ProccyBoi/kiku/Mechanical/concepts/01_Mame_front.png

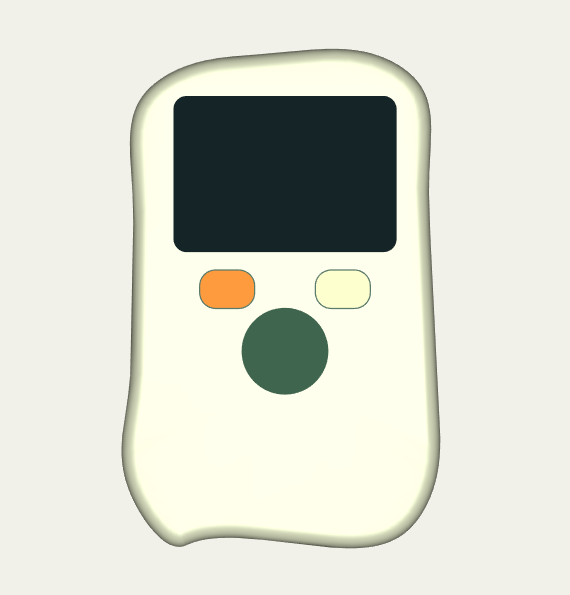
Mechanical/concepts/01_Mame_front.png
