ProccyBoi/kiku/Mechanical/concepts/01_Mame_rear.png

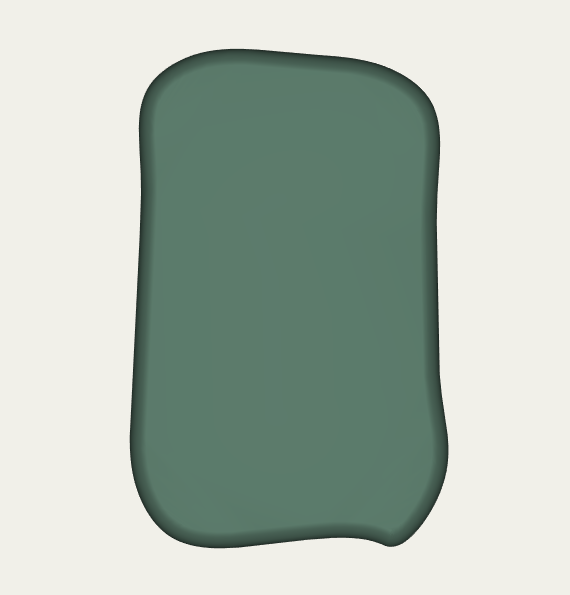
Mechanical/concepts/01_Mame_rear.png
