ProccyBoi/kiku/Mechanical/concepts/01_Mame_side.png

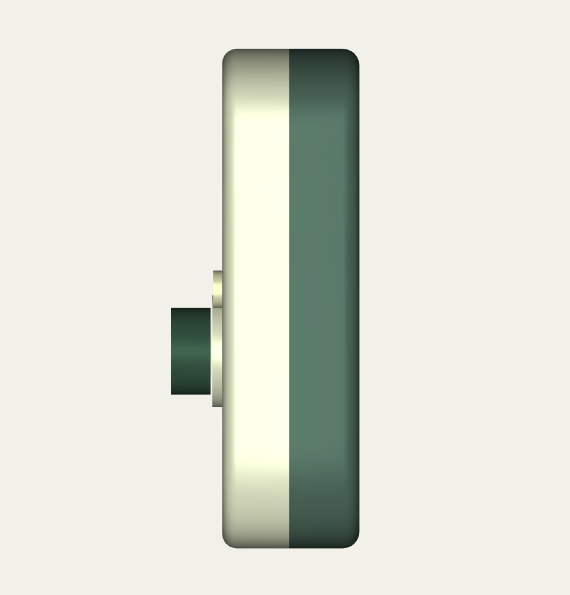
Mechanical/concepts/01_Mame_side.png
