ProccyBoi/kiku/Mechanical/concepts/02_Nagare_front.png

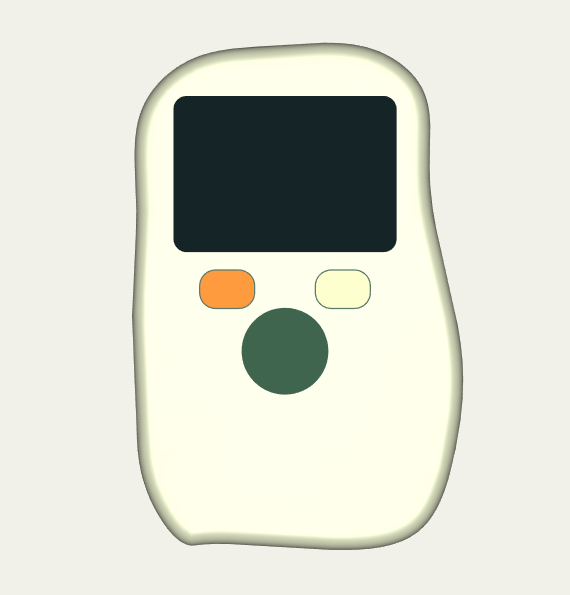
Mechanical/concepts/02_Nagare_front.png
