ProccyBoi/kiku/Mechanical/concepts/02_Nagare_rear.png

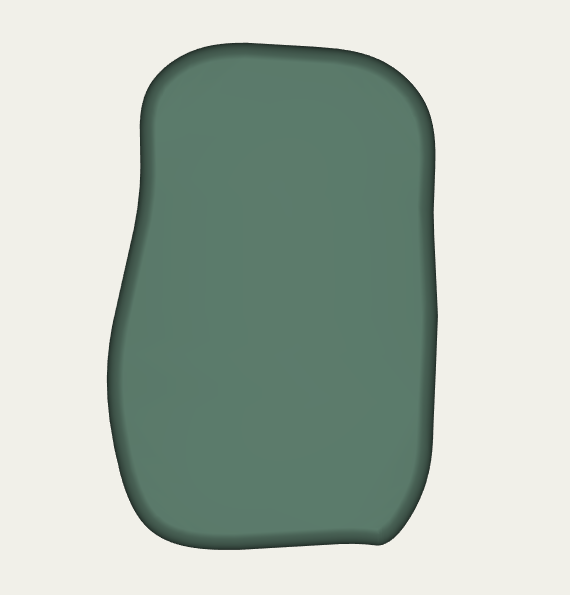
Mechanical/concepts/02_Nagare_rear.png
