ProccyBoi/kiku/Mechanical/concepts/03_Mini_rear.png

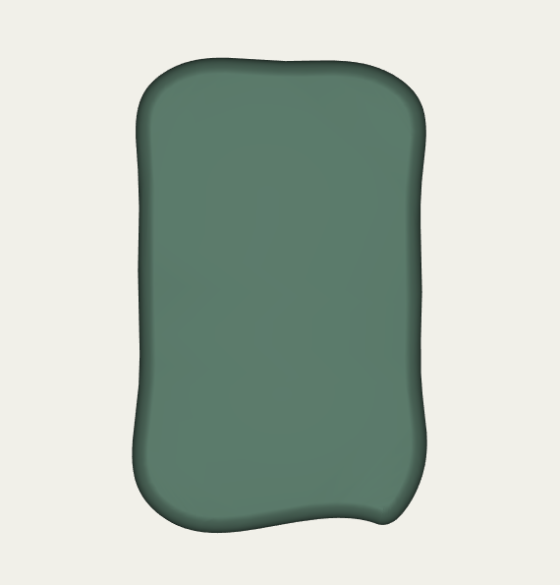
Mechanical/concepts/03_Mini_rear.png
