ProccyBoi/kiku/Mechanical/review/kiku_housing_v1_exploded.png

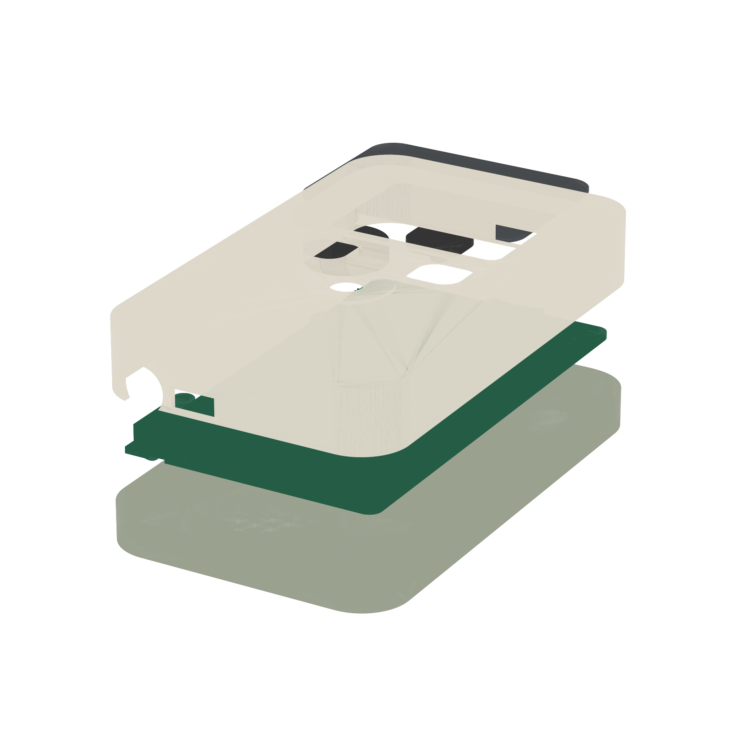
Mechanical/review/kiku_housing_v1_exploded.png
