ProccyBoi/kiku/Mechanical/review/kiku_housing_v1_front_3q.png

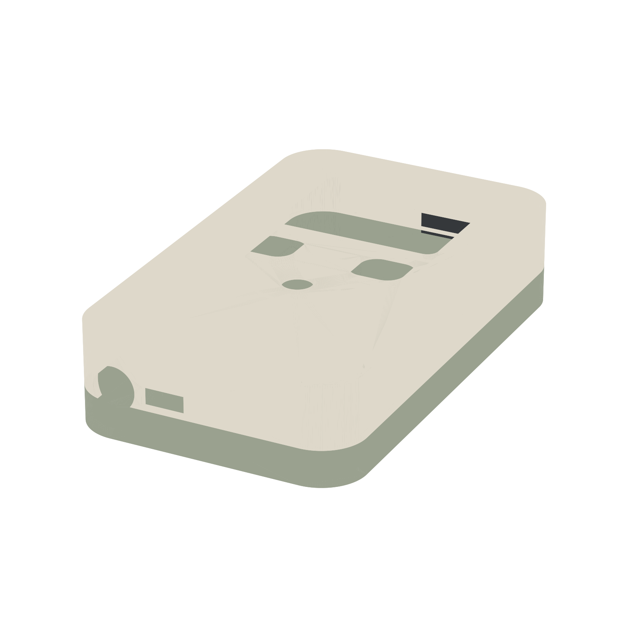
Mechanical/review/kiku_housing_v1_front_3q.png
