ProccyBoi/kiku/Mechanical/review/kiku_housing_v1_rear_3q.png

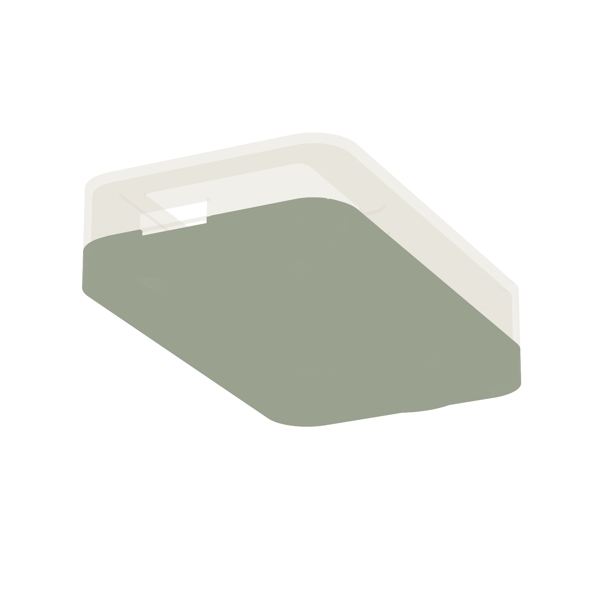
Mechanical/review/kiku_housing_v1_rear_3q.png
