ProccyBoi/kiku/Mechanical/review/kiku_housing_v6_stand_open.png

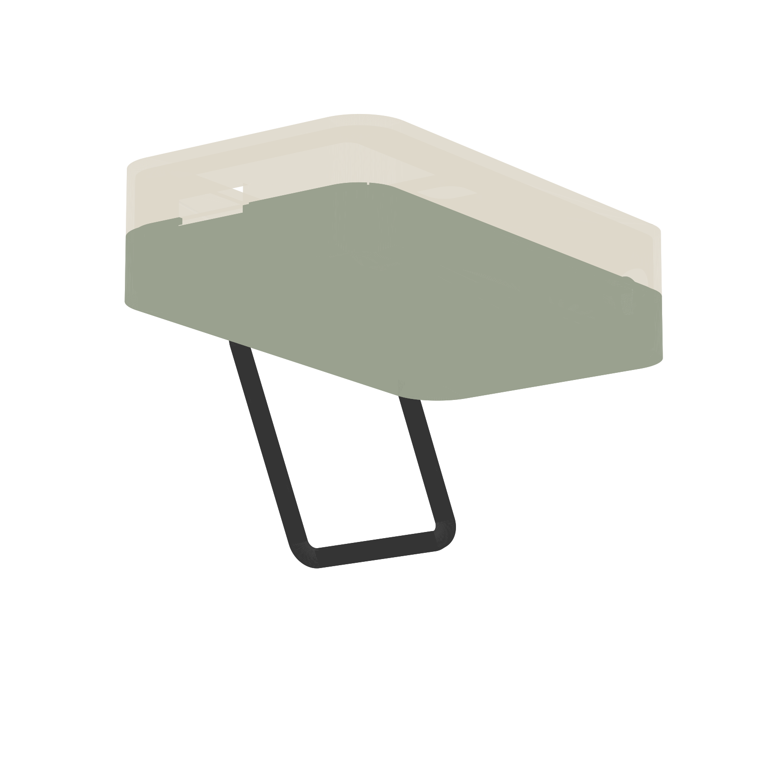
Mechanical/review/kiku_housing_v6_stand_open.png
