ProccyBoi/kiku/Mechanical/review/kiku_housing_v7_controls_closeup.png

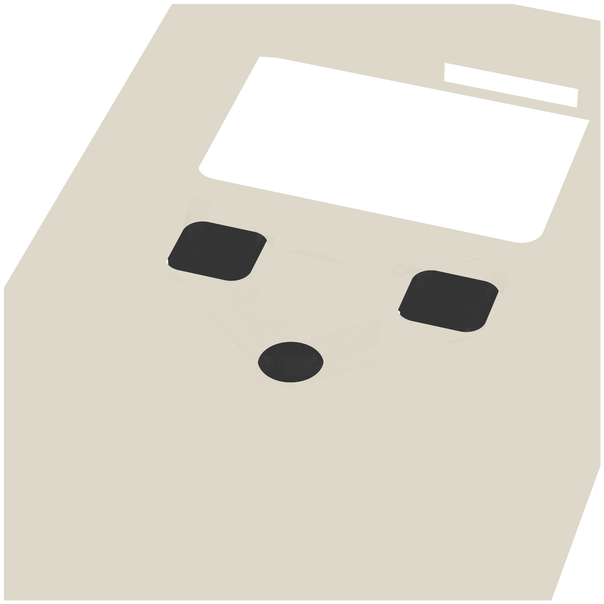
Mechanical/review/kiku_housing_v7_controls_closeup.png
