ProccyBoi/kiku/Mechanical/review/P1_antenna_route.png

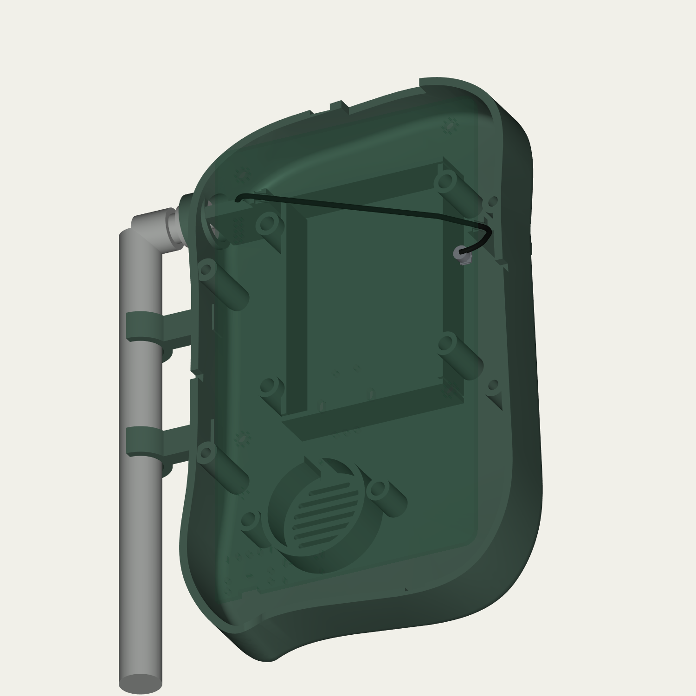
Mechanical/review/P1_antenna_route.png
