ProccyBoi/kiku/Mechanical/exports/P0/front_shell.step

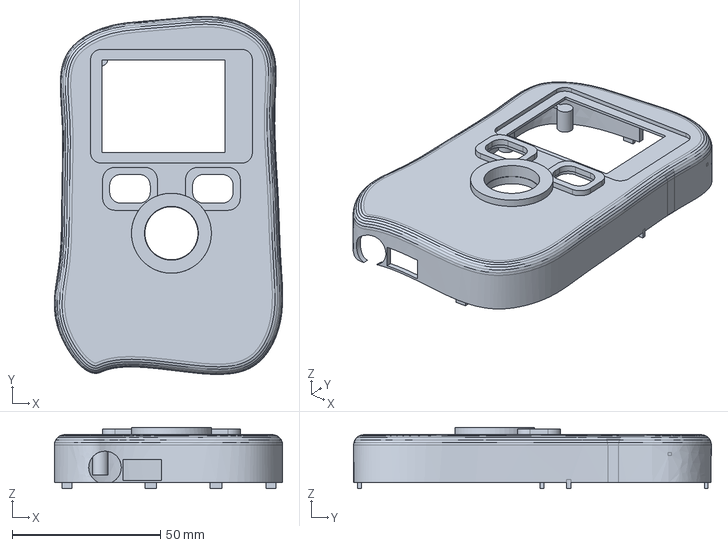
[picture p42: CAD file, 2026-09-17]
Mechanical/exports/P0/front_shell.step
77.1 x 120.9 x 20.6 mm
