ProccyBoi/kiku/Mechanical/concepts/03_Mini_front_shell.stl

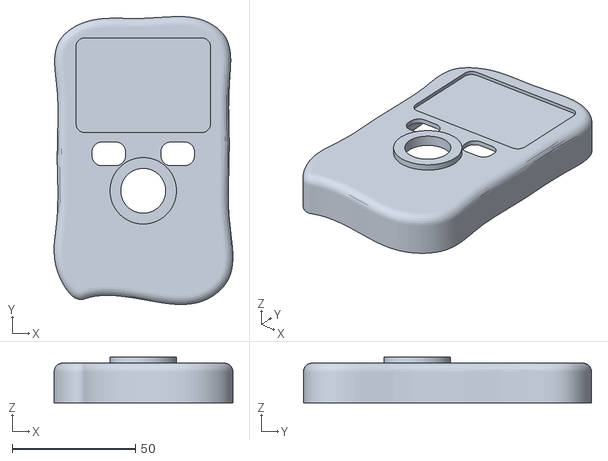
[picture p43: CAD file, 2026-09-17]
Mechanical/concepts/03_Mini_front_shell.stl
72.7 x 117.0 x 18.6
