ProccyBoi/kiku/Mechanical/exports/P0/encoder_knob.step

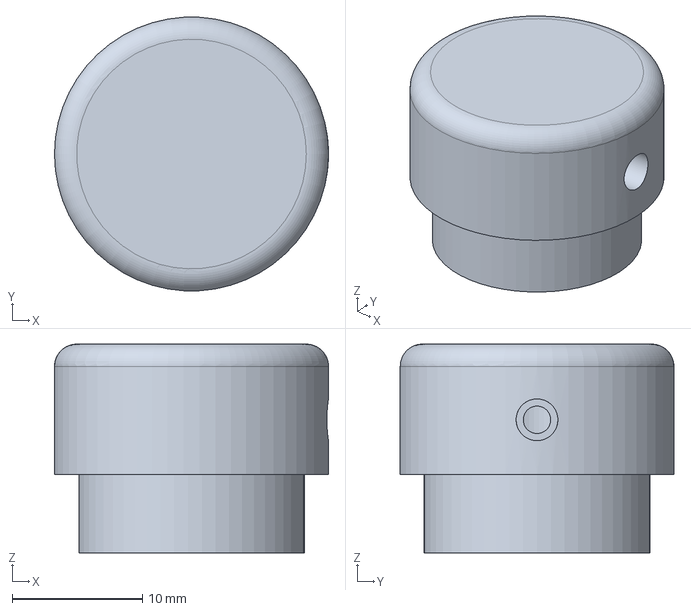
[picture p44: CAD file, 2026-09-17]
Mechanical/exports/P0/encoder_knob.step
21.0 x 21.0 x 16.0 mm
