ProccyBoi/kiku/Mechanical/concepts/02_Nagare_front_shell.stl

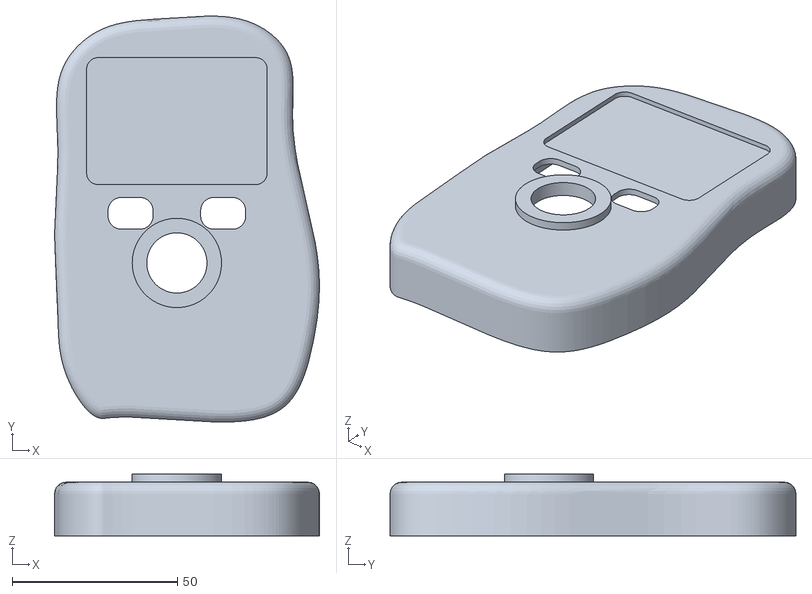
[picture p45: CAD file, 2026-09-17]
Mechanical/concepts/02_Nagare_front_shell.stl
80.1 x 122.7 x 18.6
