ProccyBoi/kiku/Mechanical/exports/kiku_button_right_v8.step

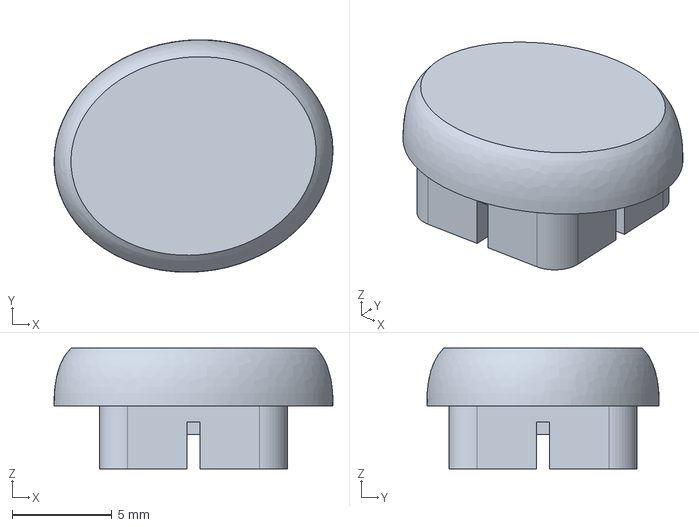
[picture p46: CAD file, 2026-09-17]
Mechanical/exports/kiku_button_right_v8.step
14.0 x 11.6 x 6.05 mm
