ProccyBoi/kiku/Mechanical/concepts/03_Mini.step

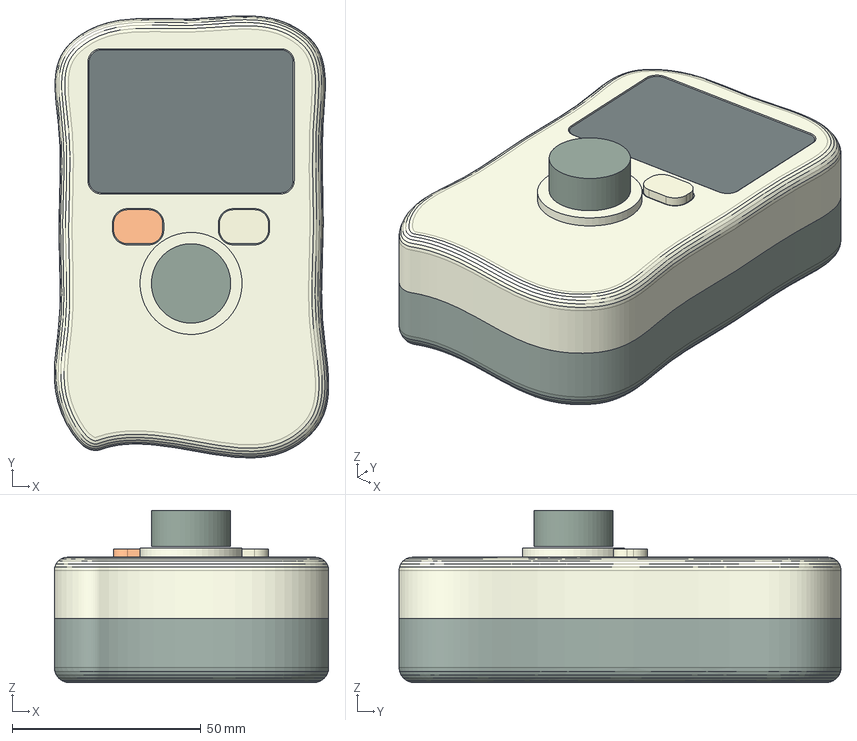
[picture p47: CAD file, 2026-09-17]
Mechanical/concepts/03_Mini.step
72.6 x 116.9 x 45.6 mm
front_shell
rear_shell
lens
button_left
button_right
encoder_knob
