ProccyBoi/kiku/Mechanical/concepts/01_Mame_rear_shell.stl

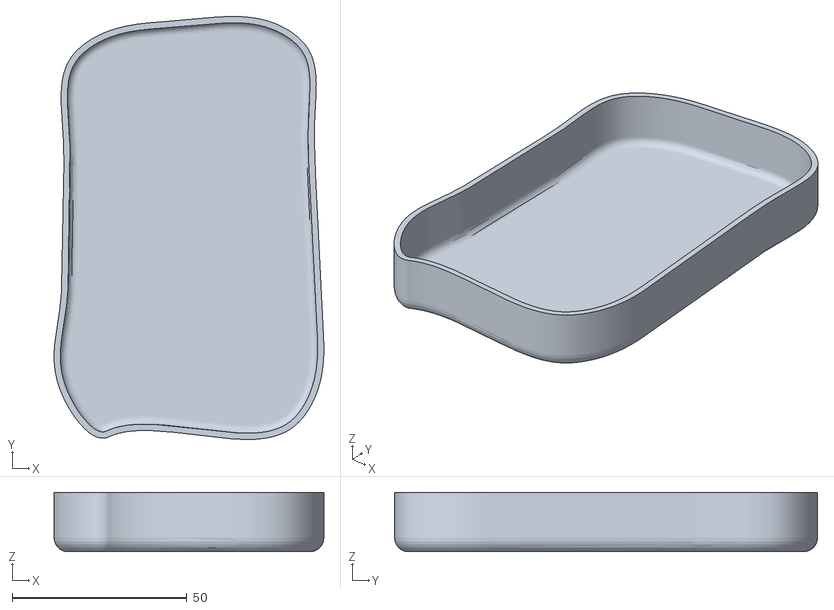
[picture p48: CAD file, 2026-09-17]
Mechanical/concepts/01_Mame_rear_shell.stl
77.1 x 120.9 x 17.0
