ProccyBoi/kiku/Mechanical/exports/kiku_front_shell_C49247039_v5.step

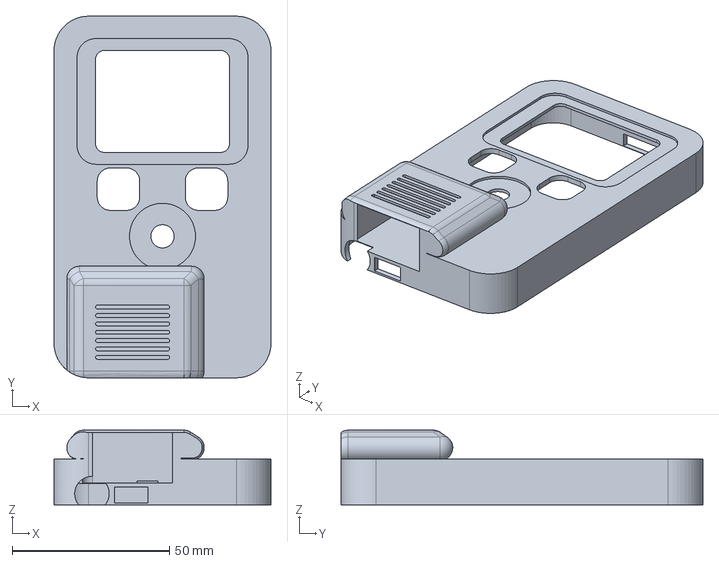
[picture p49: CAD file, 2026-09-17]
Mechanical/exports/kiku_front_shell_C49247039_v5.step
69.0 x 115.0 x 23.7 mm
