ProccyBoi/kiku/Mechanical/concepts/03_Mini_rear_shell.stl

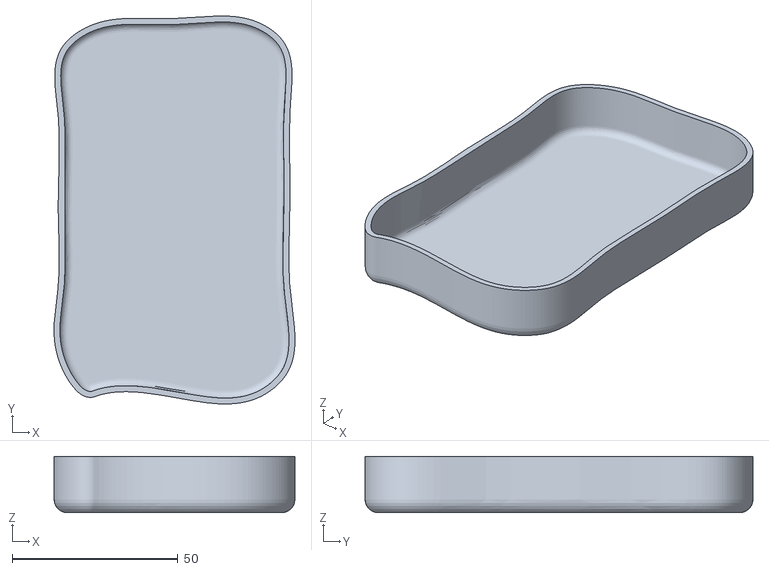
[picture p50: CAD file, 2026-09-17]
Mechanical/concepts/03_Mini_rear_shell.stl
72.7 x 117.0 x 17.0
