ProccyBoi/kiku/Mechanical/concepts/03_Mini_encoder_knob.stl

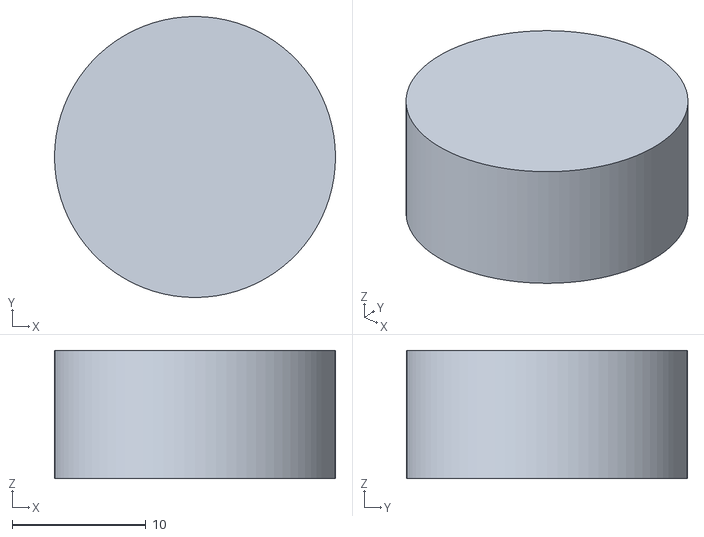
[picture p51: CAD file, 2026-09-17]
Mechanical/concepts/03_Mini_encoder_knob.stl
21.0 x 21.0 x 9.60
