ProccyBoi/kiku/Mechanical/exports/kiku_screen_lens_v8.step

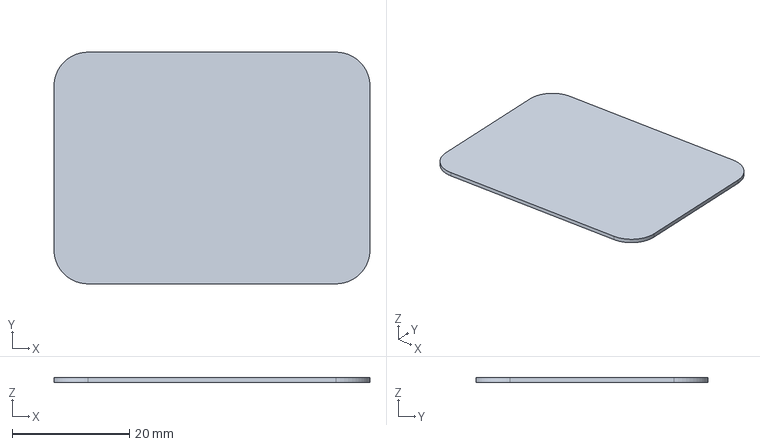
[picture p52: CAD file, 2026-09-17]
Mechanical/exports/kiku_screen_lens_v8.step
54.0 x 39.6 x 0.8 mm
