ProccyBoi/kiku/Mechanical/concepts/02_Nagare.step

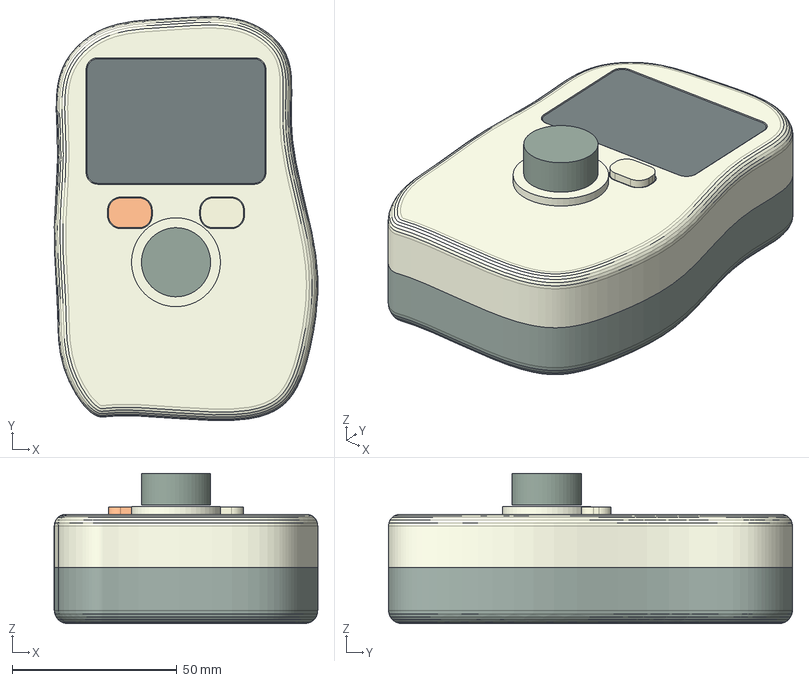
[picture p54: CAD file, 2026-09-17]
Mechanical/concepts/02_Nagare.step
80.0 x 122.7 x 45.6 mm
front_shell
rear_shell
lens
button_left
button_right
encoder_knob
