ProccyBoi/kiku/Mechanical/exports/P1/display_carrier.step

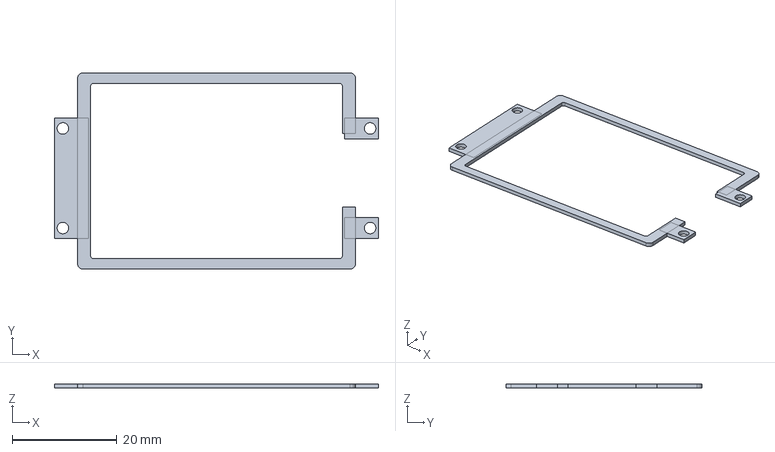
[picture p55: CAD file, 2026-09-17]
Mechanical/exports/P1/display_carrier.step
61.8 x 37.4 x 0.8 mm
