ProccyBoi/kiku/Mechanical/exports/P1/speaker_rear_foam.step

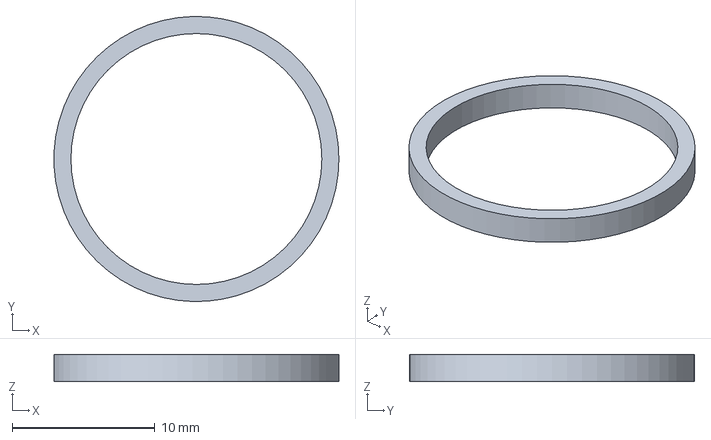
[picture p56: CAD file, 2026-09-17]
Mechanical/exports/P1/speaker_rear_foam.step
20.0 x 20.0 x 1.90 mm
