ProccyBoi/kiku/Mechanical/exports/kiku_speaker_C49247039_envelope_v5.step

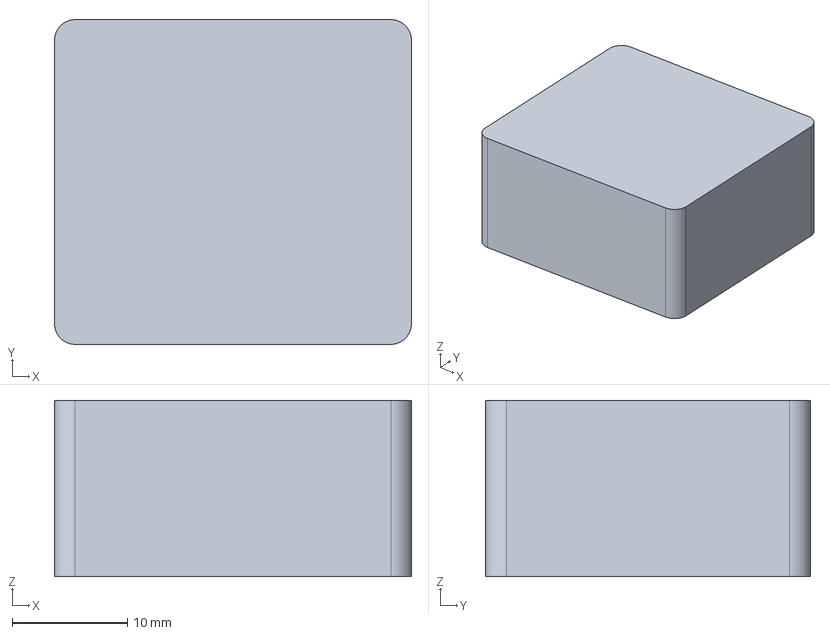
[picture p57: CAD file, 2026-09-17]
Mechanical/exports/kiku_speaker_C49247039_envelope_v5.step
31.0 x 28.2 x 15.3 mm
