ProccyBoi/kiku/Mechanical/exports/P0/battery_foam.step

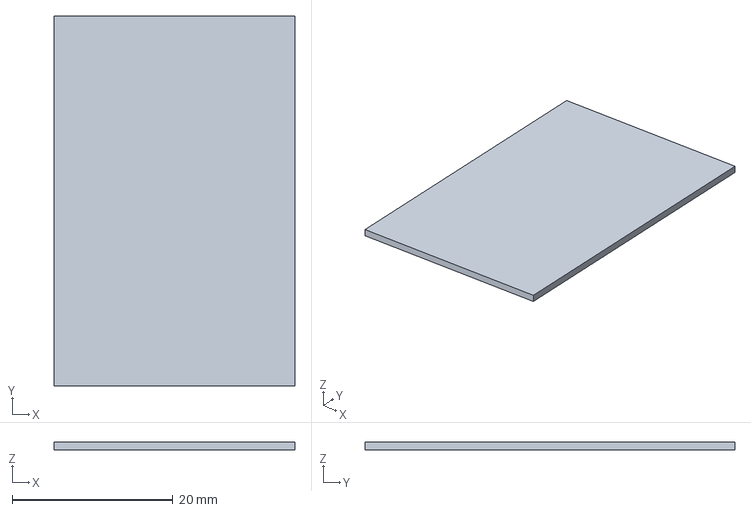
[picture p58: CAD file, 2026-09-17]
Mechanical/exports/P0/battery_foam.step
30.0 x 46.0 x 1.00 mm
