ProccyBoi/kiku/Mechanical/exports/P0/speaker_retainer.step

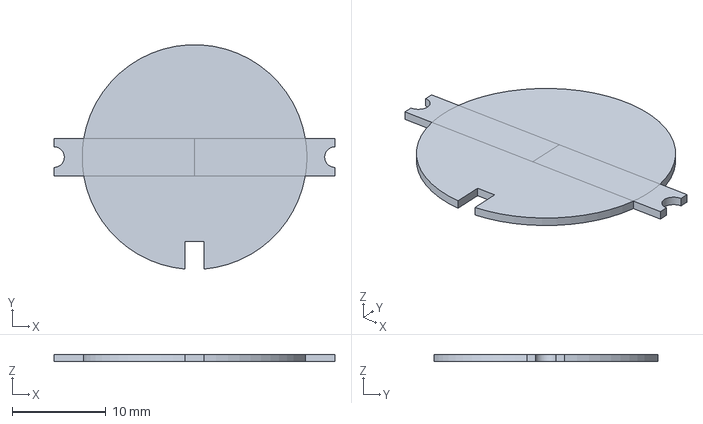
[picture p59: CAD file, 2026-09-17]
Mechanical/exports/P0/speaker_retainer.step
30.0 x 23.9 x 0.8 mm
