ProccyBoi/kiku/Mechanical/exports/kiku_rear_shell_FM_SMA_v5.step

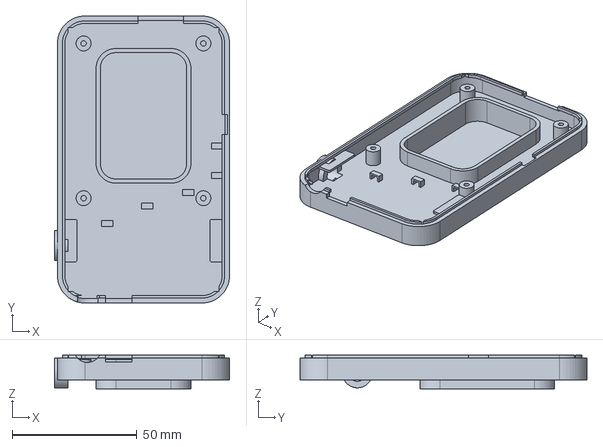
[picture p60: CAD file, 2026-09-17]
Mechanical/exports/kiku_rear_shell_FM_SMA_v5.step
70.2 x 115.0 x 13.5 mm
