ProccyBoi/kiku/Mechanical/exports/P1/speaker_rim_gasket.step

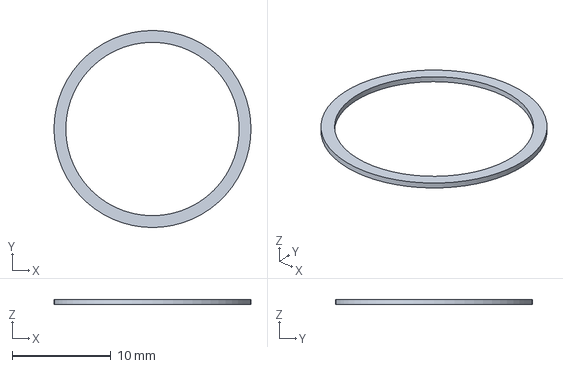
[picture p61: CAD file, 2026-09-17]
Mechanical/exports/P1/speaker_rim_gasket.step
20.0 x 20.0 x 0.5 mm
