ProccyBoi/kiku/Mechanical/exports/P1/Kiku_P1_housing.step

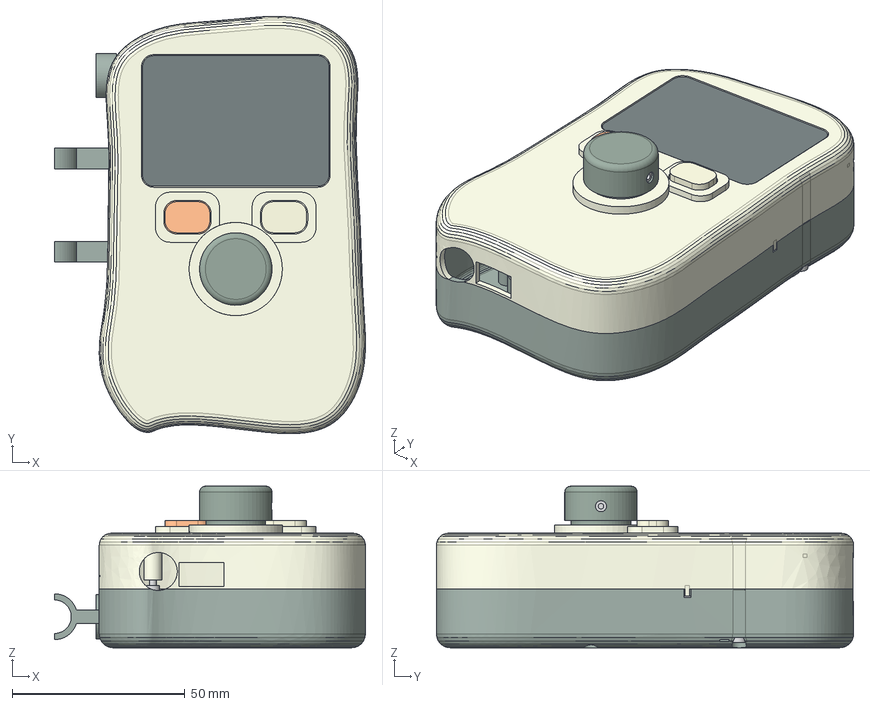
[picture p62: CAD file, 2026-09-17]
Mechanical/exports/P1/Kiku_P1_housing.step
90.1 x 120.9 x 46.8 mm
lcd_screw_0.7_72
lcd_insert_0.7_72
lcd_screw_0.7_91
lcd_insert_0.7_91
lcd_screw_59.3_72
lcd_insert_59.3_72
lcd_screw_59.3_91
lcd_insert_59.3_91
display_carrier
PCB_screw_H5
PCB_insert_H5
PCB_screw_H6
PCB_insert_H6
PCB_screw_H7
PCB_insert_H7
PCB_screw_H8
PCB_insert_H8
case_screw_1
case_insert_1
case_screw_2
case_insert_2
case_screw_3
case_insert_3
case_screw_4
case_insert_4
button_left
button_right
knob_insert
knob_grub_screw
encoder_knob
guard_screw_9.4_51
guard_insert_9.4_51
guard_screw_9.4_89
guard_insert_9.4_89
guard_screw_50.6_51
guard_insert_50.6_51
guard_screw_50.6_89
guard_insert_50.6_89
battery_guard
speaker_screw_3
speaker_insert_3
speaker_screw_33
speaker_insert_33
speaker_retainer
speaker_rim_gasket
speaker_rear_foam
battery_foam
front_shell
rear_shell
lens
