ProccyBoi/kiku/Mechanical/exports/kiku_front_shell_external_speaker_v8.step

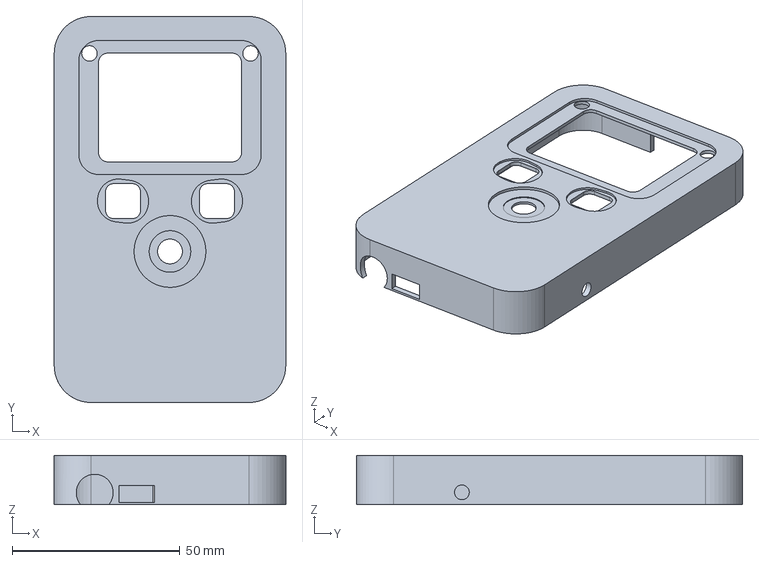
[picture p63: CAD file, 2026-09-17]
Mechanical/exports/kiku_front_shell_external_speaker_v8.step
69.0 x 115.0 x 14.6 mm
