ProccyBoi/kiku/Mechanical/exports/P0/encoder_guide.step

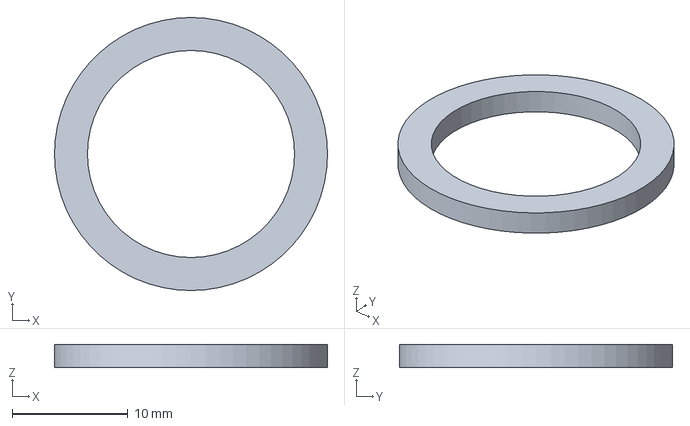
[picture p64: CAD file, 2026-09-17]
Mechanical/exports/P0/encoder_guide.step
23.6 x 23.6 x 2.00 mm
