ProccyBoi/kiku/Mechanical/exports/kiku_speaker_adapter_C50387209_v1.step

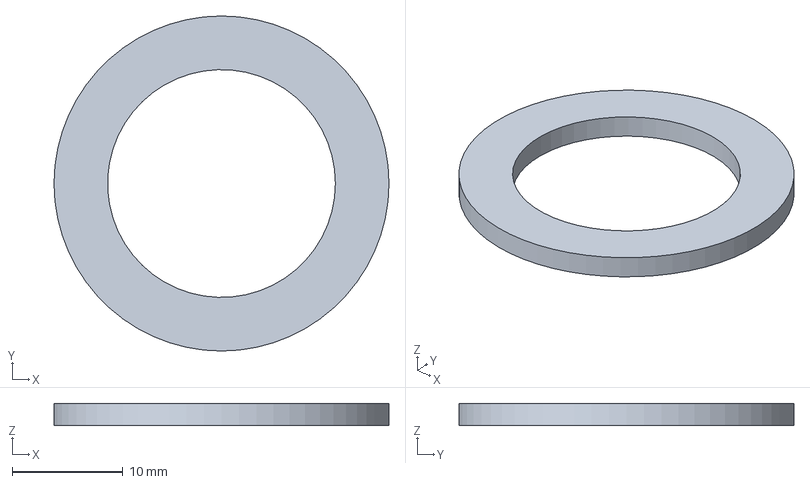
[picture p65: CAD file, 2026-09-17]
Mechanical/exports/kiku_speaker_adapter_C50387209_v1.step
30.3 x 30.3 x 2.00 mm
