ProccyBoi/kiku/Mechanical/exports/P0/rear_shell.step

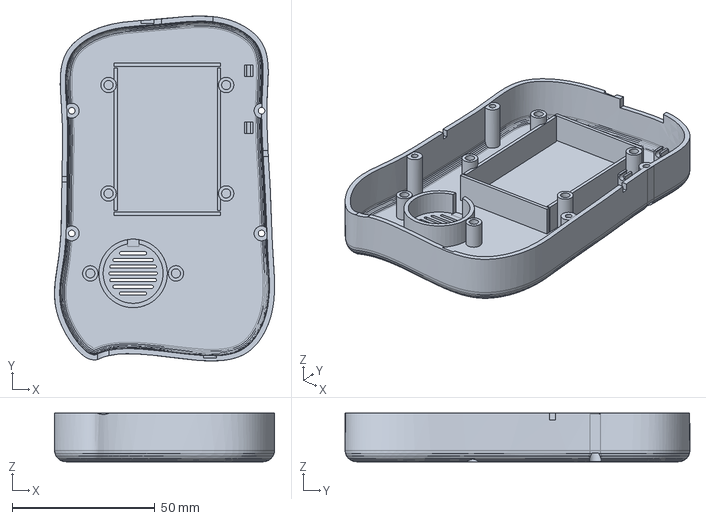
[picture p66: CAD file, 2026-09-17]
Mechanical/exports/P0/rear_shell.step
77.1 x 120.9 x 17.0 mm
