ProccyBoi/kiku/Mechanical/exports/kiku_rear_shell_v1.step

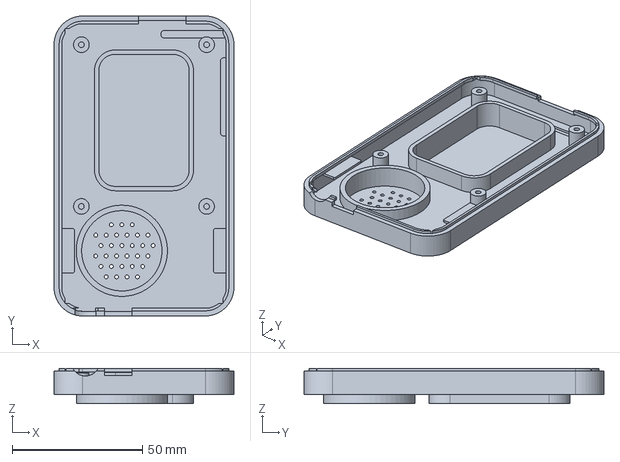
[picture p67: CAD file, 2026-09-17]
Mechanical/exports/kiku_rear_shell_v1.step
69.0 x 115.0 x 13.5 mm
