ProccyBoi/kiku/Mechanical/exports/P0/power_button.step

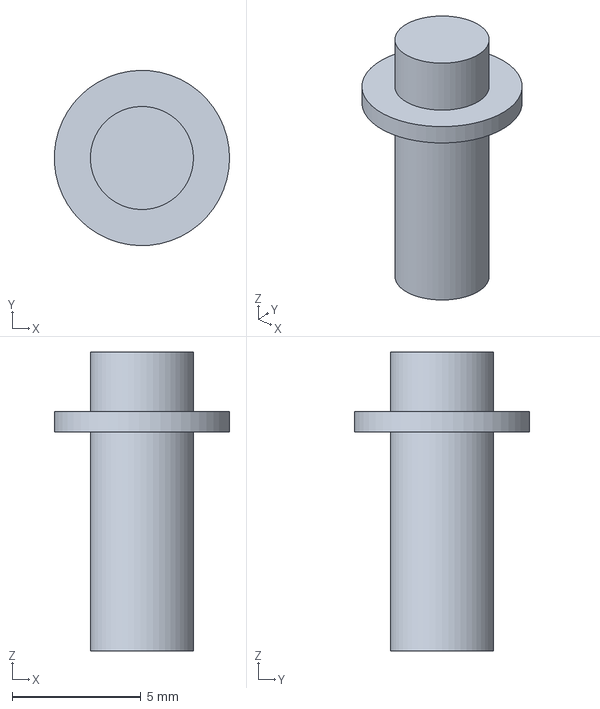
[picture p68: CAD file, 2026-09-17]
Mechanical/exports/P0/power_button.step
6.79 x 6.80 x 11.6 mm
