ProccyBoi/kiku/Mechanical/exports/kiku_encoder_knob_v8.step

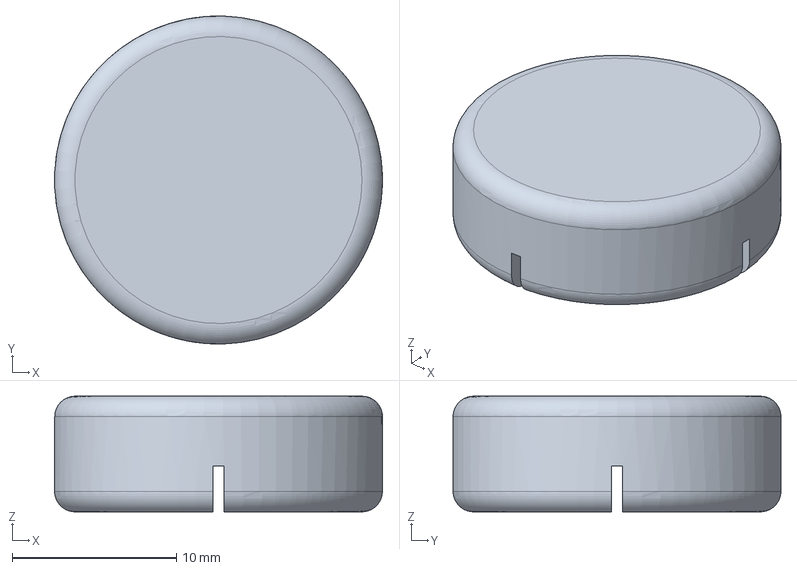
[picture p69: CAD file, 2026-09-17]
Mechanical/exports/kiku_encoder_knob_v8.step
20.0 x 20.0 x 7.05 mm
