ProccyBoi/kiku/Mechanical/exports/kiku_front_shell_C50387209_v2.step

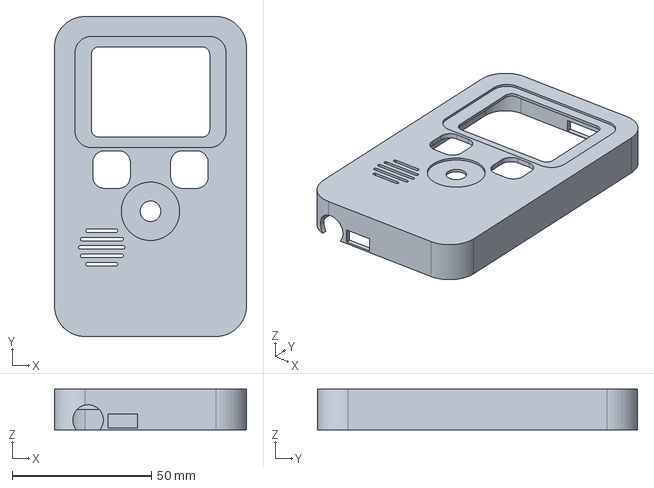
[picture p70: CAD file, 2026-09-17]
Mechanical/exports/kiku_front_shell_C50387209_v2.step
69.0 x 115.0 x 14.6 mm
