ProccyBoi/kiku/Mechanical/exports/kiku_packaging_keepouts_v8.step

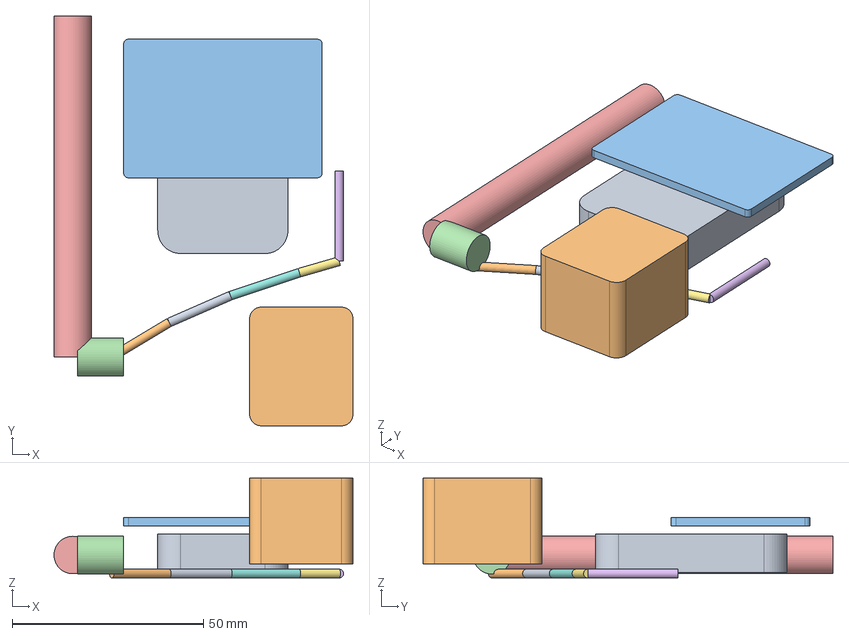
[picture p71: CAD file, 2026-09-17]
Mechanical/exports/kiku_packaging_keepouts_v8.step
78.1 x 107.0 x 26.1 mm
