ProccyBoi/kiku/Mechanical/exports/kiku_kickstand_v8.step

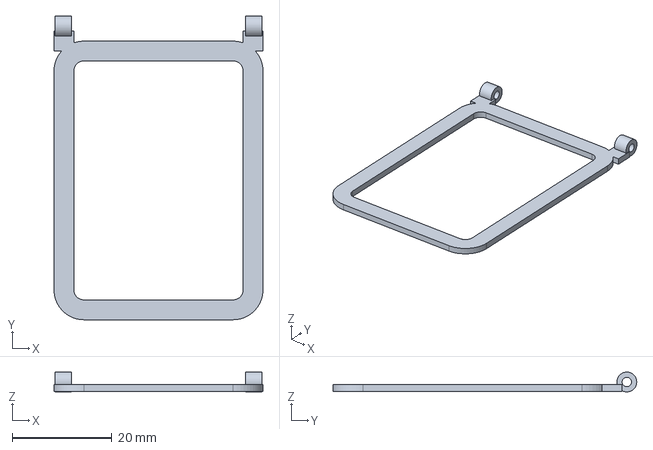
[picture p72: CAD file, 2026-09-17]
Mechanical/exports/kiku_kickstand_v8.step
42.0 x 61.0 x 4.00 mm
