ProccyBoi/kiku/Mechanical/review/P1_assembled_front.png

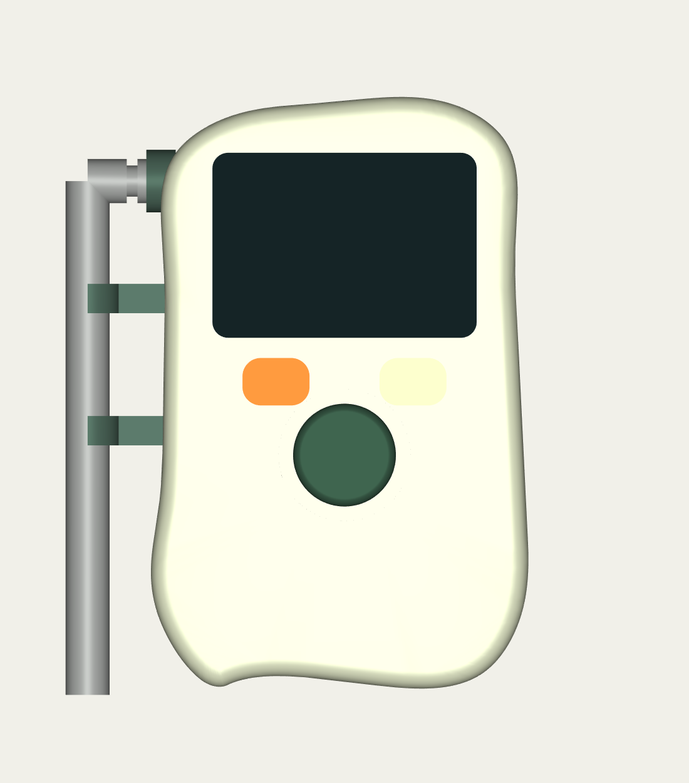
Mechanical/review/P1_assembled_front.png
