ProccyBoi/kiku/Mechanical/review/P1_assembled_iso.png

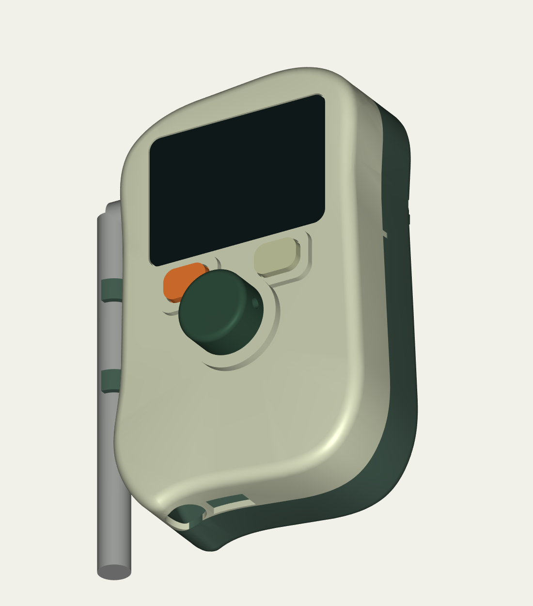
Mechanical/review/P1_assembled_iso.png
