ProccyBoi/kiku/Mechanical/review/P1_assembled_rear.png

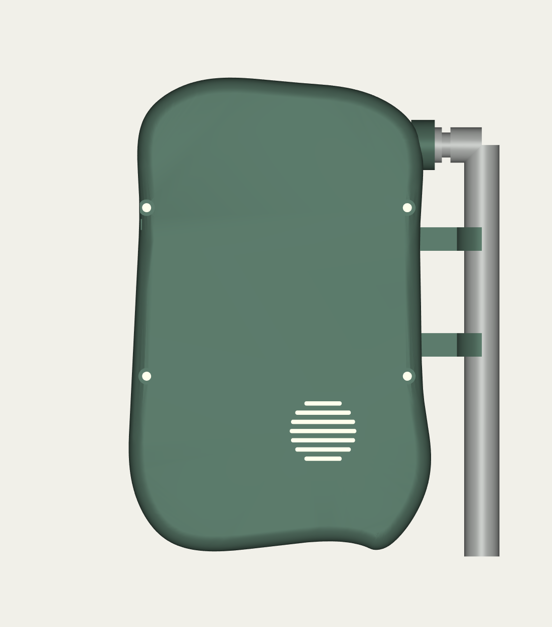
Mechanical/review/P1_assembled_rear.png
