ProccyBoi/kiku/Firmware/tests/test_main.c

#include <assert.h>
#include <stdbool.h>
#include <stddef.h>
#include <stdint.h>
#include <stdio.h>
#include <string.h>

#include "bm83.h"
#include "bt_rx_watchdog.h"
#include "bq25895.h"
#include "fm_state.h"
#include "input_manager.h"
#include "local_playback.h"
#include "settings.h"
#include "ui_renderer.h"

/* Exercise the actual application metadata scheduler and response parser. */
#include "../App/Src/app.c"

#define UI_TEST_WIDTH 320U
#define UI_TEST_HEIGHT 240U

static uint16_t s_ui_pixels[UI_TEST_WIDTH * UI_TEST_HEIGHT];
static size_t s_ui_pixel_count;
static uint16_t s_ui_window_x0;
static uint16_t s_ui_window_y0;
static uint16_t s_ui_window_x1;
static uint16_t s_ui_window_y1;
static size_t s_ui_window_cursor;

dev_status_t st7789_startup_sequence(st7789_t *lcd)
{
    (void)lcd;
    return DEV_ENOTSUP;
}

dev_status_t st7789_command(st7789_t *lcd, uint8_t command,
                           const uint8_t *data, size_t len)
{
    (void)lcd; (void)command; (void)data; (void)len;
    return DEV_ENOTSUP;
}

dev_status_t st7789_set_window(st7789_t *lcd, uint16_t x0, uint16_t y0,
                               uint16_t x1, uint16_t y1)
{
    assert(lcd != NULL);
    assert(x0 <= x1 && y0 <= y1);
    assert(x1 < lcd->width && y1 < lcd->height);
    s_ui_window_x0 = x0;
    s_ui_window_y0 = y0;
    s_ui_window_x1 = x1;
    s_ui_window_y1 = y1;
    s_ui_window_cursor = 0U;
    s_ui_pixel_count = 0U;
    return DEV_OK;
}

dev_status_t st7789_write_pixels_rgb565(st7789_t *lcd,
                                        const uint16_t *pixels, size_t count)
{
    assert(lcd != NULL && pixels != NULL);
    size_t width = (size_t)s_ui_window_x1 - s_ui_window_x0 + 1U;
    size_t height = (size_t)s_ui_window_y1 - s_ui_window_y0 + 1U;
    assert(s_ui_window_cursor + count <= width * height);
    for (size_t i = 0U; i < count; ++i) {
        size_t pos = s_ui_window_cursor + i;
        size_t x = (size_t)s_ui_window_x0 + (pos % width);
        size_t y = (size_t)s_ui_window_y0 + (pos / width);
        assert(x < lcd->width && y < lcd->height);
        s_ui_pixels[y * UI_TEST_WIDTH + x] = pixels[i];
    }
    s_ui_window_cursor += count;
    s_ui_pixel_count += count;
    return DEV_OK;
}

static uint32_t ui_frame_hash(void)
{
    uint32_t h = 2166136261UL;
    for (size_t i = 0U; i < sizeof(s_ui_pixels) / sizeof(s_ui_pixels[0]); ++i) {
        h ^= s_ui_pixels[i];
        h *= 16777619UL;
    }
    return h;
}

static uint32_t ui_structure_hash(void)
{
    /* Structural signature independent of palette: (0,0) is always untouched
     * theme paper, so hash only whether each rendered pixel differs from it. */
    uint16_t paper = s_ui_pixels[0];
    uint32_t h = 2166136261UL;
    for (size_t i = 0U; i < sizeof(s_ui_pixels) / sizeof(s_ui_pixels[0]); ++i) {
        h ^= s_ui_pixels[i] == paper ? 0U : 1U;
        h *= 16777619UL;
    }
    return h;
}

typedef struct {
    bool b1_level;
    bool b2_level;
    bool enc_level;
    unsigned encoder_long_events;
    unsigned encoder_press_events;
    unsigned b1_events;
    unsigned b2_events;
    unsigned b1_long_events;
    unsigned b2_long_events;
} input_mock_t;

static bool input_gpio_read(void *ctx)
{
    return *(bool *)ctx;
}

static void input_capture(void *ctx, const input_event_t *event)
{
    input_mock_t *m = ctx;
    if (event->type == INPUT_EVENT_ENCODER_LONG) ++m->encoder_long_events;
    else if (event->type == INPUT_EVENT_ENCODER_PRESS) ++m->encoder_press_events;
    else if (event->type == INPUT_EVENT_BUTTON_1) ++m->b1_events;
    else if (event->type == INPUT_EVENT_BUTTON_2) ++m->b2_events;
    else if (event->type == INPUT_EVENT_BUTTON_1_LONG) ++m->b1_long_events;
    else if (event->type == INPUT_EVENT_BUTTON_2_LONG) ++m->b2_long_events;
}

static void test_input_encoder_long_power_gesture(void)
{
    input_mock_t m = { .b1_level = true, .b2_level = true, .enc_level = true };
    dev_gpio_t b1 = { .ctx = &m.b1_level, .read = input_gpio_read };
    dev_gpio_t b2 = { .ctx = &m.b2_level, .read = input_gpio_read };
    dev_gpio_t enc = { .ctx = &m.enc_level, .read = input_gpio_read };
    input_manager_t mgr;
    assert(input_manager_init(&mgr, &b1, &b2, &enc, true, 25U, 900U, 4000U,
                              input_capture, &m) == DEV_OK);

    input_manager_poll(&mgr, 0U);

    /* Power is exclusively a deliberate four-second encoder hold. It fires
     * once while held and suppresses the release-time short/back press. */
    m.enc_level = false;
    input_manager_poll(&mgr, 10U);
    input_manager_poll(&mgr, 40U);
    input_manager_poll(&mgr, 4039U);
    assert(m.encoder_long_events == 0U);
    input_manager_poll(&mgr, 4040U);
    assert(m.encoder_long_events == 1U);
    input_manager_poll(&mgr, 4200U);
    assert(m.encoder_long_events == 1U);
    m.enc_level = true;
    input_manager_poll(&mgr, 4210U);
    input_manager_poll(&mgr, 4240U);
    assert(m.encoder_press_events == 0U);

    /* A normal encoder click is still emitted promptly on release; users do not
     * need to wait for the four-second power threshold to navigate back. */
    m.enc_level = false;
    input_manager_poll(&mgr, 4260U);
    input_manager_poll(&mgr, 4290U);
    m.enc_level = true;
    input_manager_poll(&mgr, 4390U);
    input_manager_poll(&mgr, 4420U);
    assert(m.encoder_press_events == 1U);

    /* Pressing both front buttons no longer has any hidden power meaning. */
    m.b1_level = false; m.b2_level = false;
    input_manager_poll(&mgr, 4500U);
    input_manager_poll(&mgr, 4530U);
    m.b1_level = true; m.b2_level = true;
    input_manager_poll(&mgr, 4550U);
    input_manager_poll(&mgr, 4580U);
    assert(m.encoder_long_events == 1U);
    assert(m.b1_events == 1U && m.b2_events == 1U);

    /* A normal isolated B1 press remains a normal short press afterwards. */
    m.b1_level = false;
    input_manager_poll(&mgr, 4650U);
    input_manager_poll(&mgr, 4680U);
    m.b1_level = true;
    input_manager_poll(&mgr, 4700U);
    input_manager_poll(&mgr, 4730U);
    assert(m.b1_events == 2U);

    /* B1 is the dedicated long-hold Back gesture. It fires once and suppresses
     * the release-time B1 short event. */
    m.b1_level = false;
    input_manager_poll(&mgr, 5800U);
    input_manager_poll(&mgr, 5830U);
    input_manager_poll(&mgr, 6729U);
    assert(m.b1_long_events == 0U);
    input_manager_poll(&mgr, 6730U);
    assert(m.b1_long_events == 1U);
    m.b1_level = true;
    input_manager_poll(&mgr, 6750U);
    input_manager_poll(&mgr, 6780U);
    assert(m.b1_events == 2U);

    /* B2 keeps its contextual long action and also suppresses its short event
     * when the long threshold was reached. */
    m.b2_level = false;
    input_manager_poll(&mgr, 6800U);
    input_manager_poll(&mgr, 6830U);
    input_manager_poll(&mgr, 7730U);
    assert(m.b2_long_events == 1U);
    m.b2_level = true;
    input_manager_poll(&mgr, 7750U);
    input_manager_poll(&mgr, 7780U);
    assert(m.b2_events == 1U);
}

typedef struct {
    uint8_t frame[512];
    size_t frame_len;
    unsigned writes;
    bool mfb;
    unsigned mfb_highs;
    unsigned mfb_lows;
    uint32_t delayed_ms;
    uint32_t now_ms;
    bool reset_n;
    unsigned reset_lows;
    unsigned reset_highs;
} bm_mock_t;

static dev_status_t mock_uart_write(void *ctx, const uint8_t *data, size_t len, uint32_t timeout_ms)
{
    bm_mock_t *m = ctx;
    (void)timeout_ms;
    assert(len <= sizeof(m->frame));
    memcpy(m->frame, data, len);
    m->frame_len = len;
    ++m->writes;
    return DEV_OK;
}

static void mock_gpio_write(void *ctx, bool level)
{
    bm_mock_t *m = ctx;
    m->mfb = level;
    if (level) ++m->mfb_highs; else ++m->mfb_lows;
}

static void mock_delay(void *ctx, uint32_t ms)
{
    bm_mock_t *m = ctx;
    m->delayed_ms += ms;
    m->now_ms += ms;
}

static uint32_t mock_time(void *ctx)
{
    return ((bm_mock_t *)ctx)->now_ms;
}

static void mock_reset_write(void *ctx, bool level)
{
    bm_mock_t *m = ctx;
    m->reset_n = level;
    if (level) ++m->reset_highs; else ++m->reset_lows;
}

typedef struct {
    unsigned calls;
    bm83_packet_t packet;
} packet_capture_t;

static void packet_cb(void *ctx, const bm83_packet_t *packet)
{
    packet_capture_t *cap = ctx;
    ++cap->calls;
    cap->packet = *packet;
}

static void make_v206_text_response(bm83_packet_t *packet, bool end_of_body,
                                    const uint8_t *attributes,
                                    const char *const *values, size_t count)
{
    assert(packet != NULL && attributes != NULL && values != NULL && count <= 7U);
    memset(packet, 0, sizeof(*packet));
    packet->id = BM83_EVENT_AVRCP_VENDOR_DEPENDENT_RSP;
    packet->payload[0] = 0x20U;
    packet->payload[1] = 0x00U;
    packet->payload[2] = 0x04U;
    packet->payload[3] = end_of_body ? 1U : 0U;
    packet->payload[4] = (uint8_t)count;

    size_t pos = 7U;
    for (size_t i = 0U; i < count; ++i) {
        size_t len = strlen(values[i]);
        assert(pos + 8U + len <= sizeof(packet->payload));
        packet->payload[pos + 0U] = 0U;
        packet->payload[pos + 1U] = 0U;
        packet->payload[pos + 2U] = 0U;
        packet->payload[pos + 3U] = attributes[i];
        packet->payload[pos + 4U] = 0U;
        packet->payload[pos + 5U] = 0x6AU;
        packet->payload[pos + 6U] = (uint8_t)(len >> 8);
        packet->payload[pos + 7U] = (uint8_t)len;
        memcpy(&packet->payload[pos + 8U], values[i], len);
        pos += 8U + len;
    }
    size_t list_len = pos - 7U;
    packet->payload[5] = (uint8_t)(list_len >> 8);
    packet->payload[6] = (uint8_t)list_len;
    packet->payload_len = (uint16_t)pos;
}

static void test_app_metadata_fallback(void)
{
    bm_mock_t m = {0};
    dev_uart_bus_t uart = { .ctx = &m, .write = mock_uart_write };
    dev_clock_t clock = { .ctx = &m, .time_ms = mock_time };
    bm83_t dev;
    assert(bm83_init(&dev, &uart, NULL, NULL, NULL, &clock) == DEV_OK);
    kiku_app_t app = {0};
    app.deps.bluetooth = &dev;
    settings_defaults(&app.settings.value);
    ui_state_init(&app.ui, &app.settings.value);
    /* An unknown/2.02 module must never enter optional browsing, but the
     * production BM83 project is live-proven to accept the 0x4A metadata path
     * despite reporting UART v2.02. */
    app_mark_avrcp_available(&app, 0U);
    assert(app.bt_browse_stage == BT_BROWSE_IDLE);
    app.bt_avrcp_capability_pending = false;
    app.bt_track_notification_pending = false;
    app_service_bt_metadata_transport(&app, 10000U);
    assert(m.frame[3] == BM83_CMD_AVRCP_VENDOR_DEPENDENT);
    assert(m.frame[4] == 0x00U);
    assert(m.frame[5] == 0x20U);
    assert(m.frame[6] == 0x01U);
    assert(m.frame[10] == 1U);
    /* This test only verifies the fallback frame here; complete the synthetic
     * request before moving on to independent parser/browsing cases. */
    app_bt_metadata_end_request(&app, 10000U, true);
    dev.awaiting_command_ack = false;

    /* Parse real legacy response framing and retain separately polled fields. */
    bm83_packet_t packet = { .id = BM83_EVENT_AVC_VENDOR_DEPENDENT_RESPONSE };
    const uint8_t title[] = {0,0x0C,0x48,0,0,0x19,0x58,0x20,0,0,13,
                             1,0,0,0,1,0,0x6A,0,4,'S','o','n','g'};
    memcpy(packet.payload, title, sizeof(title));
    packet.payload_len = sizeof(title);
    app_parse_bm83_metadata(&app, &packet);
    assert(strcmp(app.ui.track_title, "Song") == 0);
    packet.payload[15] = 2U;
    memcpy(&packet.payload[20], "Band", 4U);
    app_parse_bm83_metadata(&app, &packet);
    assert(strcmp(app.ui.track_title, "Song") == 0);
    assert(strcmp(app.ui.track_artist, "Band") == 0);

    /* Even a discovered player can lose browsing. Every wait must fall back. */
    const uint8_t waits[] = { BT_BROWSE_WAIT_PLAYER_LIST, BT_BROWSE_WAIT_SET_ADDRESSED,
        BT_BROWSE_WAIT_SET_BROWSED, BT_BROWSE_WAIT_NOW_PLAYING,
        BT_BROWSE_WAIT_TRACK_ATTRIBUTES };
    dev.uart_version_valid = true;
    dev.uart_version_major = 2U; dev.uart_version_minor = 6U;
    for (size_t i = 0; i < sizeof(waits); ++i) {
        dev.awaiting_command_ack = false;
        app_bt_metadata_reset_transaction(&app, 20000U, false);
        app.bt_browse_stage = waits[i];
        app.bt_player_id = 7U;
        app.bt_player_valid = true;
        app.last_bt_browse_request_ms = 0U;
        app_service_bt_metadata_transport(&app, 20000U);
        assert(app.bt_browse_stage == BT_BROWSE_IDLE);
        assert(!app.bt_player_valid);
        assert(m.frame[3] == BM83_CMD_AVRCP_VENDOR_DEPENDENT);
        /* This loop is testing independent browsing timeout states, not an
         * intentionally abandoned 0x4A. Finish the synthetic fallback request
         * before constructing the next case so stale-drain state cannot leak
         * between otherwise unrelated fixtures. */
        if (app.bt_metadata_request_inflight) {
            app_bt_metadata_end_request(&app, 20000U, true);
        }
        app.bt_metadata_discard_response = false;
    }
}

static void test_app_metadata_response_scheduler(void)
{
    bm_mock_t m = { .now_ms = 1000U };
    dev_uart_bus_t uart = { .ctx = &m, .write = mock_uart_write };
    dev_clock_t clock = { .ctx = &m, .time_ms = mock_time };
    bm83_t dev;
    assert(bm83_init(&dev, &uart, NULL, NULL, NULL, &clock) == DEV_OK);

    kiku_app_t app = {0};
    app.deps.bluetooth = &dev;
    app.deps.clock = clock;
    app.audio.source = AUDIO_SOURCE_BLUETOOTH;
    settings_defaults(&app.settings.value);
    ui_state_init(&app.ui, &app.settings.value);
    ui_state_set_track(&app.ui, "Old title", "Old artist", "Old album");
    bm83_set_packet_callback(&dev, app_bm83_packet, &app);

    uint32_t requests_before = g_bt_metadata_diag.metadata_request_count;
    uint32_t completes_before = g_bt_metadata_diag.metadata_core_complete_count;
    uint32_t changes_before = g_bt_metadata_diag.metadata_core_change_count;
    uint32_t timeouts_before = g_bt_metadata_diag.metadata_timeout_count;

    app_mark_avrcp_available(&app, 0U);
    app.bt_avrcp_capability_pending = false;
    app.bt_track_notification_pending = false;
    app_service_bt_metadata_transport(&app, m.now_ms);
    assert(app.bt_metadata_request_inflight);
    assert(app.bt_metadata_request_kind == BT_METADATA_REQ_CORE);
    assert(m.frame[3] == BM83_CMD_AVRCP_VENDOR_DEPENDENT);
    assert(m.frame[6] == 0x01U && m.frame[10] == 0x01U);
    assert(g_bt_metadata_diag.metadata_request_count == requests_before + 1U);

    /* A Command_ACK releases the UART slot, but not the logical metadata
     * transaction. No second 0x4A may be issued before the actual 0x5D body. */
    const uint8_t metadata_ack[] = {0xAA,0x00,0x03,0x00,0x4A,0x00,0xB3};
    bm83_rx_data(&dev, metadata_ack, sizeof(metadata_ack));
    unsigned writes_after_ack = m.writes;
    m.now_ms += 100U;
    app_service_bt_metadata_transport(&app, m.now_ms);
    assert(app.bt_metadata_request_inflight);
    assert(m.writes == writes_after_ack);

    /* Each field-proven 0x4A physical transaction requests exactly one identity
     * attribute. The logical title/artist/album cycle stages all three and only
     * commits after the album response, so the UI can never cross-mix tracks. */
    bm83_packet_t fragment;
    const uint8_t title_attr[] = {1U};
    const char *const title_value[] = {"Song"};
    make_v206_text_response(&fragment, true, title_attr, title_value, 1U);
    app_parse_bm83_metadata_v206(&app, &fragment);
    assert(strcmp(app.ui.track_title, "Old title") == 0);
    assert(strcmp(app.ui.track_artist, "Old artist") == 0);
    assert(strcmp(app.ui.track_album, "Old album") == 0);
    assert(!app.bt_metadata_request_inflight);
    assert(app.bt_metadata_core_next_attribute == 2U);
    assert(app.bt_metadata_stage_seen_mask == 0x01U);

    m.now_ms = app.bt_metadata_next_due_ms;
    app_service_bt_metadata_transport(&app, m.now_ms);
    assert(app.bt_metadata_request_inflight);
    assert(m.frame[6] == 0x01U && m.frame[10] == 0x02U);
    bm83_rx_data(&dev, metadata_ack, sizeof(metadata_ack));
    const uint8_t artist_attr[] = {2U};
    const char *const artist_value[] = {"Band"};
    make_v206_text_response(&fragment, true, artist_attr, artist_value, 1U);
    app_parse_bm83_metadata_v206(&app, &fragment);
    assert(!app.bt_metadata_request_inflight);
    assert(app.bt_metadata_core_next_attribute == 3U);
    assert(app.bt_metadata_stage_seen_mask == 0x03U);
    assert(strcmp(app.ui.track_title, "Old title") == 0);
    assert(strcmp(app.ui.track_artist, "Old artist") == 0);
    assert(strcmp(app.ui.track_album, "Old album") == 0);

    m.now_ms = app.bt_metadata_next_due_ms;
    app_service_bt_metadata_transport(&app, m.now_ms);
    assert(app.bt_metadata_request_inflight);
    assert(m.frame[6] == 0x01U && m.frame[10] == 0x03U);
    bm83_rx_data(&dev, metadata_ack, sizeof(metadata_ack));
    const uint8_t album_attr[] = {3U};
    const char *const album_value[] = {"Album"};
    make_v206_text_response(&fragment, true, album_attr, album_value, 1U);
    app_parse_bm83_metadata_v206(&app, &fragment);
    assert(strcmp(app.ui.track_title, "Song") == 0);
    assert(strcmp(app.ui.track_artist, "Band") == 0);
    assert(strcmp(app.ui.track_album, "Album") == 0);
    assert(!app.bt_metadata_request_inflight);
    assert(app.bt_metadata_core_next_attribute == 0U);
    assert(!app.bt_metadata_force_core);
    assert(g_bt_metadata_diag.metadata_core_complete_count == completes_before + 1U);
    assert(g_bt_metadata_diag.metadata_core_change_count == changes_before + 1U);

    /* Notifications are accelerators, not correctness dependencies. With no
     * notification at all, the periodic core deadline must issue another
     * atomic identity cycle. */
    m.now_ms += APP_BT_METADATA_CORE_POLL_MS - 1U;
    unsigned writes_before_periodic = m.writes;
    app_service_bt_metadata_transport(&app, m.now_ms);
    assert(m.writes == writes_before_periodic);
    ++m.now_ms;
    app_service_bt_metadata_transport(&app, m.now_ms);
    assert(app.bt_metadata_request_inflight);
    assert(m.frame[3] == BM83_CMD_AVRCP_VENDOR_DEPENDENT &&
           m.frame[6] == 0x01U && m.frame[10] == 0x01U);

    /* A Command_ACK means BTM owns the physical AVRCP transaction. If its 0x5D
     * goes missing, never compound the fault by submitting another 0x4A. Keep
     * the accepted transaction stalled until its late response or a real profile
     * boundary proves the old transaction can no longer complete. */
    bm83_rx_data(&dev, metadata_ack, sizeof(metadata_ack));
    const uint32_t timed_request_started = app.bt_metadata_request_started_ms;
    m.now_ms = timed_request_started + APP_BT_METADATA_RESPONSE_TIMEOUT_MS;
    app_service_bt_metadata_transport(&app, m.now_ms);
    assert(app.bt_metadata_request_inflight);
    assert(app.bt_metadata_command_accepted);
    assert(app.bt_metadata_response_stalled);
    assert(g_bt_metadata_diag.metadata_timeout_count == timeouts_before + 1U);
    unsigned writes_after_timeout = m.writes;
    m.now_ms += APP_BT_METADATA_RETRY_BACKOFF_MS * 4U;
    app_service_bt_metadata_transport(&app, m.now_ms);
    assert(m.writes == writes_after_timeout);

    /* A late response still closes the exact accepted physical transaction and
     * advances the logical cycle without exposing a partial identity. */
    const char *const late_title_value[] = {"Late title"};
    make_v206_text_response(&fragment, true, title_attr, late_title_value, 1U);
    app_parse_bm83_metadata_v206(&app, &fragment);
    assert(!app.bt_metadata_request_inflight);
    assert(!app.bt_metadata_response_stalled);
    assert(app.bt_metadata_core_next_attribute == 2U);
    assert(strcmp(app.ui.track_title, "Song") == 0);

    /* A local track step can overtake a metadata response after the 0x4A UART
     * ACK. Clear the visible identity immediately and discard the late old-song
     * response instead of repopulating it. */
    m.now_ms = app.bt_metadata_next_due_ms;
    app_service_bt_metadata_transport(&app, m.now_ms);
    assert(app.bt_metadata_request_inflight && app.bt_metadata_requested_attribute == 2U);
    bm83_rx_data(&dev, metadata_ack, sizeof(metadata_ack));
    ui_state_set_track(&app.ui, "Current", "Artist", "Record");
    assert(kiku_app_bluetooth_music_action(&app, BM83_MUSIC_NEXT) == DEV_OK);
    assert(app.bt_metadata_discard_response);
    assert(app.ui.track_title[0] == '\0');
    const uint8_t old_artist_attr[] = {2U};
    const char *const old_artist_value[] = {"Wrong"};
    make_v206_text_response(&fragment, true, old_artist_attr, old_artist_value, 1U);
    app_parse_bm83_metadata_v206(&app, &fragment);
    assert(app.ui.track_title[0] == '\0');
    assert(app.ui.track_artist[0] == '\0');
    assert(app.ui.track_album[0] == '\0');
    assert(!app.bt_metadata_request_inflight);
    assert(app.bt_metadata_force_core);

    /* Finish the NEXT UART transaction and issue the fresh request. Even though
     * this is no longer the pre-NEXT transaction, the phone can briefly return
     * the same old identity while its player is still settling. That identity
     * must remain quarantined rather than flashing back onto the screen. */
    const uint8_t music_ack[] = {0xAA,0x00,0x03,0x00,0x04,0x00,0xF9};
    bm83_rx_data(&dev, music_ack, sizeof(music_ack));
    m.now_ms = app.bt_metadata_next_due_ms;
    app_service_bt_metadata_transport(&app, m.now_ms);
    assert(app.bt_metadata_request_inflight);
    bm83_rx_data(&dev, metadata_ack, sizeof(metadata_ack));

    uint32_t guarded_changes = g_bt_metadata_diag.metadata_core_change_count;
    const char *const guarded_title[] = {"Current"};
    const char *const guarded_artist[] = {"Artist"};
    const char *const guarded_album[] = {"Record"};
    make_v206_text_response(&fragment, true, title_attr, guarded_title, 1U);
    app_parse_bm83_metadata_v206(&app, &fragment);
    m.now_ms = app.bt_metadata_next_due_ms;
    app_service_bt_metadata_transport(&app, m.now_ms);
    bm83_rx_data(&dev, metadata_ack, sizeof(metadata_ack));
    make_v206_text_response(&fragment, true, artist_attr, guarded_artist, 1U);
    app_parse_bm83_metadata_v206(&app, &fragment);
    m.now_ms = app.bt_metadata_next_due_ms;
    app_service_bt_metadata_transport(&app, m.now_ms);
    bm83_rx_data(&dev, metadata_ack, sizeof(metadata_ack));
    make_v206_text_response(&fragment, true, album_attr, guarded_album, 1U);
    app_parse_bm83_metadata_v206(&app, &fragment);
    assert(app.ui.track_title[0] == '\0');
    assert(app.ui.track_artist[0] == '\0');
    assert(app.ui.track_album[0] == '\0');
    assert(app.bt_metadata_identity_guard_active);
    assert(g_bt_metadata_diag.metadata_core_change_count == guarded_changes);

    m.now_ms = app.bt_metadata_next_due_ms;
    app_service_bt_metadata_transport(&app, m.now_ms);
    assert(app.bt_metadata_request_inflight);
    bm83_rx_data(&dev, metadata_ack, sizeof(metadata_ack));
    const char *const next_title[] = {"Next song"};
    const char *const next_artist[] = {"New artist"};
    const char *const next_album[] = {"New album"};
    make_v206_text_response(&fragment, true, title_attr, next_title, 1U);
    app_parse_bm83_metadata_v206(&app, &fragment);
    m.now_ms = app.bt_metadata_next_due_ms;
    app_service_bt_metadata_transport(&app, m.now_ms);
    bm83_rx_data(&dev, metadata_ack, sizeof(metadata_ack));
    make_v206_text_response(&fragment, true, artist_attr, next_artist, 1U);
    app_parse_bm83_metadata_v206(&app, &fragment);
    m.now_ms = app.bt_metadata_next_due_ms;
    app_service_bt_metadata_transport(&app, m.now_ms);
    bm83_rx_data(&dev, metadata_ack, sizeof(metadata_ack));
    make_v206_text_response(&fragment, true, album_attr, next_album, 1U);
    app_parse_bm83_metadata_v206(&app, &fragment);
    assert(strcmp(app.ui.track_title, "Next song") == 0);
    assert(strcmp(app.ui.track_artist, "New artist") == 0);
    assert(strcmp(app.ui.track_album, "New album") == 0);
    assert(!app.bt_metadata_identity_guard_active);
    assert(g_bt_metadata_diag.metadata_core_change_count == guarded_changes + 1U);

    /* Start another core request so a profile-loss reset abandons a real
     * accepted 0x4A response. The stale-drain quarantine must survive both
     * disconnect and immediate AVRCP re-entry. */
    m.now_ms = app.bt_metadata_next_due_ms;
    app_service_bt_metadata_transport(&app, m.now_ms);
    assert(app.bt_metadata_request_inflight);
    bm83_rx_data(&dev, metadata_ack, sizeof(metadata_ack));

    bm83_packet_t disconnect = { .id = BM83_EVENT_BTM_STATUS, .payload_len = 2U };
    disconnect.payload[0] = BM83_BTM_A2DP_DISCONNECTED;
    disconnect.payload[1] = 0U;
    app_bm83_packet(&app, &disconnect);
    assert(!app.bt_metadata_request_inflight);
    assert(app.bt_metadata_discard_response);
    assert(!app.bt_avrcp_connected);

    app_mark_avrcp_available(&app, 0U);
    app.bt_avrcp_capability_pending = false;
    app.bt_track_notification_pending = false;
    assert(app.bt_metadata_discard_response);
    unsigned writes_before_reentry = m.writes;
    app_service_bt_metadata_transport(&app, m.now_ms);
    assert(m.writes == writes_before_reentry);

    /* Drain the abandoned pre-disconnect result. It must not become the first
     * song after reconnect, and only after that drain may a fresh core query run. */
    const char *const stale_title[] = {"Stale"};
    make_v206_text_response(&fragment, true, title_attr, stale_title, 1U);
    app_parse_bm83_metadata_v206(&app, &fragment);
    assert(!app.bt_metadata_discard_response);
    assert(app.ui.track_title[0] == '\0');
    m.now_ms = app.bt_metadata_next_due_ms;
    app_service_bt_metadata_transport(&app, m.now_ms);
    assert(app.bt_metadata_request_inflight);

    /* Exercise Memory Full through the actual application callback, not just the
     * driver. The rejected 0x4A ends this logical attempt, but the driver must
     * hold the exact command behind the documented ready gate until BM83 later
     * emits 0x4A/status-0. Human transport controls remain usable meanwhile. */
    bm83_set_packet_callback(&dev, app_bm83_packet, &app);
    uint32_t backpressure_before = g_bt_metadata_diag.metadata_backpressure_count;
    const uint8_t memory_full_ack[] = {0xAA,0x00,0x03,0x00,0x4A,0x05,0xAE};
    bm83_rx_data(&dev, memory_full_ack, sizeof(memory_full_ack));
    assert(!app.bt_metadata_request_inflight);
    assert(app.bt_metadata_force_core);
    assert(app.bt_metadata_next_due_ms == m.now_ms + APP_BT_METADATA_RETRY_BACKOFF_MS);
    assert(g_bt_metadata_diag.metadata_backpressure_count == backpressure_before + 1U);
    assert(!dev.awaiting_command_ack);
    assert(bm83_command_waiting_ready(&dev, BM83_CMD_AVRCP_VENDOR_DEPENDENT));
    assert(!dev.command_error_latched);

    /* Passing the application's ordinary retry deadline must not generate a
     * polling storm while BM83 still owns the backpressure gate. */
    unsigned writes_while_backpressured = m.writes;
    m.now_ms = app.bt_metadata_next_due_ms;
    app_service_bt_metadata_transport(&app, m.now_ms);
    assert(m.writes == writes_while_backpressured);
    assert(!app.bt_metadata_request_inflight);

    /* The gate is command-specific: an unrelated playback control is allowed
     * through immediately and can be ACKed independently. */
    assert(kiku_app_bluetooth_music_action(&app, BM83_MUSIC_PLAY) == DEV_OK);
    assert(dev.awaiting_command_ack && dev.pending_command_id == BM83_CMD_MUSIC_CONTROL);
    const uint8_t play_ack[] = {0xAA,0x00,0x03,0x00,0x04,0x00,0xF9};
    bm83_rx_data(&dev, play_ack, sizeof(play_ack));
    assert(!dev.awaiting_command_ack);
    assert(bm83_command_waiting_ready(&dev, BM83_CMD_AVRCP_VENDOR_DEPENDENT));

    /* BM83's later matching status-0 ACK is a readiness notification, not the
     * completion of the rejected metadata packet. Only after it arrives may the
     * scheduler construct a fresh single-attribute 0x4A request. */
    uint32_t ready_before = g_bm83_diag.nonfatal_ready_ack_count;
    bm83_rx_data(&dev, metadata_ack, sizeof(metadata_ack));
    assert(!bm83_command_waiting_ready(&dev, BM83_CMD_AVRCP_VENDOR_DEPENDENT));
    assert(g_bm83_diag.nonfatal_ready_ack_count == ready_before + 1U);
    unsigned writes_before_ready_retry = m.writes;
    app_service_bt_metadata_transport(&app, m.now_ms);
    assert(app.bt_metadata_request_inflight);
    assert(m.writes == writes_before_ready_retry + 1U);
    assert(m.frame[3] == BM83_CMD_AVRCP_VENDOR_DEPENDENT &&
           m.frame[6] == 0x01U && m.frame[10] == 0x01U);
}

static void test_app_metadata_refresh_hints_and_track_steps(void)
{
    bm_mock_t m = { .now_ms = 4000U };
    dev_uart_bus_t uart = { .ctx = &m, .write = mock_uart_write };
    dev_clock_t clock = { .ctx = &m, .time_ms = mock_time };
    bm83_t dev;
    assert(bm83_init(&dev, &uart, NULL, NULL, NULL, &clock) == DEV_OK);

    kiku_app_t app = {0};
    app.deps.bluetooth = &dev;
    app.deps.clock = clock;
    app.audio.source = AUDIO_SOURCE_BLUETOOTH;
    settings_defaults(&app.settings.value);
    ui_state_init(&app.ui, &app.settings.value);
    app_mark_avrcp_available(&app, 0U);
    app.bt_avrcp_capability_pending = false;
    app.bt_track_notification_pending = false;
    app.bt_metadata_force_core = false;
    app.bt_metadata_next_due_ms = m.now_ms + 5000U;
    ui_state_set_track(&app.ui, "Existing", "Existing artist", "Existing album");

    /* PlaybackStatusChanged is observed reliably on the fielded phone even when
     * TrackChanged is omitted. CHANGED accelerates metadata without clearing a
     * still-valid identity while INTERIM must not force a poll. */
    bm83_packet_t notification = { .id = BM83_EVENT_AVC_VENDOR_DEPENDENT_RESPONSE };
    notification.payload[0] = 0U;
    notification.payload[1] = 0x0FU; /* INTERIM */
    notification.payload[2] = 0x48U;
    notification.payload[3] = 0x00U;
    notification.payload[4] = 0x00U;
    notification.payload[5] = 0x19U;
    notification.payload[6] = 0x58U;
    notification.payload[7] = 0x31U;
    notification.payload[8] = 0x00U;
    notification.payload[9] = 0x00U;
    notification.payload[10] = 0x02U;
    notification.payload[11] = 0x01U; /* PlaybackStatusChanged */
    notification.payload[12] = 0x01U;
    notification.payload_len = 13U;
    uint32_t forced_before = g_bt_metadata_diag.metadata_forced_refresh_count;
    app_parse_bm83_notification(&app, &notification);
    assert(!app.bt_metadata_force_core);
    assert(g_bt_metadata_diag.metadata_forced_refresh_count == forced_before);

    notification.payload[1] = 0x0DU; /* CHANGED */
    app_parse_bm83_notification(&app, &notification);
    assert(app.bt_metadata_force_core);
    assert(app.bt_metadata_next_due_ms == m.now_ms + APP_BT_METADATA_POST_CONTROL_MS);
    assert(strcmp(app.ui.track_title, "Existing") == 0);
    assert(g_bt_metadata_diag.metadata_forced_refresh_count == forced_before + 1U);

    unsigned writes_before_hint = m.writes;
    m.now_ms = app.bt_metadata_next_due_ms - 1U;
    app_service_bt_metadata_transport(&app, m.now_ms);
    assert(m.writes == writes_before_hint);
    ++m.now_ms;
    app_service_bt_metadata_transport(&app, m.now_ms);
    assert(app.bt_metadata_request_inflight);
    assert(m.frame[3] == BM83_CMD_AVRCP_VENDOR_DEPENDENT &&
           m.frame[6] == 0x01U && m.frame[10] == 0x01U);
    const uint8_t metadata_ack[] = {0xAA,0x00,0x03,0x00,0x4A,0x00,0xB3};
    bm83_rx_data(&dev, metadata_ack, sizeof(metadata_ack));

    /* TrackChanged is a stronger identity boundary: clear the visible song,
     * re-register the one-shot notification and discard any pre-change 0x5D. */
    memset(&notification, 0, sizeof(notification));
    notification.id = BM83_EVENT_AVC_VENDOR_DEPENDENT_RESPONSE;
    notification.payload[0] = 0U;
    notification.payload[1] = 0x0DU;
    notification.payload[2] = 0x48U;
    notification.payload[3] = 0x00U;
    notification.payload[4] = 0x00U;
    notification.payload[5] = 0x19U;
    notification.payload[6] = 0x58U;
    notification.payload[7] = 0x31U;
    notification.payload[8] = 0x00U;
    notification.payload[9] = 0x00U;
    notification.payload[10] = 0x09U;
    notification.payload[11] = 0x02U; /* TrackChanged */
    for (size_t i = 0U; i < 8U; ++i) notification.payload[12U + i] = (uint8_t)(i + 1U);
    notification.payload_len = 20U;
    uint32_t track_changes_before = g_bt_metadata_diag.metadata_track_change_count;
    app_parse_bm83_notification(&app, &notification);
    assert(app.bt_track_notification_pending);
    assert(app.bt_metadata_discard_response);
    assert(app.ui.track_title[0] == '\0');
    assert(g_bt_metadata_diag.metadata_track_change_count == track_changes_before + 1U);

    bm83_packet_t stale;
    const uint8_t attrs[] = {1U, 2U, 3U};
    const char *const stale_values[] = {"Old phone title", "Old phone artist", "Old phone album"};
    make_v206_text_response(&stale, true, attrs, stale_values, 3U);
    app_parse_bm83_metadata_v206(&app, &stale);
    assert(app.ui.track_title[0] == '\0');
    assert(app.ui.track_artist[0] == '\0');
    assert(app.ui.track_album[0] == '\0');

    /* Both local skip directions use the same old-response quarantine. Exercise
     * each explicitly so PREVIOUS cannot regress behind NEXT-only coverage. */
    const bm83_music_action_t steps[] = { BM83_MUSIC_NEXT, BM83_MUSIC_PREVIOUS };
    const uint8_t music_ack[] = {0xAA,0x00,0x03,0x00,0x04,0x00,0xF9};
    for (size_t i = 0U; i < sizeof(steps) / sizeof(steps[0]); ++i) {
        dev.awaiting_command_ack = false;
        app.bt_track_notification_pending = false;
        app.bt_metadata_discard_response = false;
        app_bt_metadata_reset_transaction(&app, m.now_ms, true);
        app.bt_metadata_discard_response = false;
        app_service_bt_metadata_transport(&app, m.now_ms);
        assert(app.bt_metadata_request_inflight);
        bm83_rx_data(&dev, metadata_ack, sizeof(metadata_ack));
        ui_state_set_track(&app.ui, "Current", "Artist", "Album");
        assert(kiku_app_bluetooth_music_action(&app, steps[i]) == DEV_OK);
        assert(app.bt_metadata_discard_response);
        assert(app.ui.track_title[0] == '\0');
        make_v206_text_response(&stale, true, attrs, stale_values, 3U);
        app_parse_bm83_metadata_v206(&app, &stale);
        assert(app.ui.track_title[0] == '\0');
        assert(app.ui.track_artist[0] == '\0');
        assert(app.ui.track_album[0] == '\0');
        bm83_rx_data(&dev, music_ack, sizeof(music_ack));
        m.now_ms += APP_BT_METADATA_POST_CONTROL_MS;
    }
}

static void test_bm83(void)
{
    bm_mock_t m = {0};
    dev_uart_bus_t uart = { .ctx = &m, .write = mock_uart_write };
    dev_gpio_t mfb = { .ctx = &m, .read = NULL, .write = mock_gpio_write };
    dev_gpio_t reset_n = { .ctx = &m, .read = NULL, .write = mock_reset_write };
    dev_clock_t clock = { .ctx = &m, .delay_ms = mock_delay, .time_ms = mock_time };
    bm83_t dev;
    assert(bm83_init(&dev, &uart, &reset_n, &mfb, NULL, &clock) == DEV_OK);

    assert(!bm83_uart_version_at_least(&dev, 2U, 0U));
    const uint8_t uart_v202[] = {0xAA,0x00,0x04,0x18,0x00,0x02,0x02,0xE0};
    bm83_rx_data(&dev, uart_v202, sizeof(uart_v202));
    assert(dev.uart_version_valid);
    assert(dev.uart_version_major == 2U && dev.uart_version_minor == 2U);
    assert(bm83_uart_version_at_least(&dev, 2U, 0U));
    assert(bm83_uart_version_at_least(&dev, 2U, 2U));
    assert(!bm83_uart_version_at_least(&dev, 2U, 3U));
    assert(!bm83_uart_version_at_least(&dev, 3U, 0U));

    assert(bm83_unmask_all_events(&dev) == DEV_OK);
    const uint8_t expected_event_mask[] = {
        0xAA,0x00,0x05,0x03,0x00,0x00,0x00,0x00,0xF8
    };
    assert(m.frame_len == sizeof(expected_event_mask));
    assert(memcmp(m.frame, expected_event_mask, sizeof(expected_event_mask)) == 0);
    const uint8_t event_mask_ack[] = {0xAA,0x00,0x03,0x00,0x03,0x00,0xFA};
    bm83_rx_data(&dev, event_mask_ack, sizeof(event_mask_ack));
    assert(!dev.awaiting_command_ack);

    assert(bm83_music_control(&dev, BM83_MUSIC_TOGGLE) == DEV_OK);
    const uint8_t expected_music[] = {0xAA,0x00,0x03,0x04,0x00,0x07,0xF2};
    assert(m.frame_len == sizeof(expected_music));
    assert(memcmp(m.frame, expected_music, sizeof(expected_music)) == 0);
    /* BM83 has no UART_RX_IND input. Normal UART traffic must never pulse MFB;
     * on this module MFB is a real button/control pin. */
    assert(m.mfb_highs == 0U && m.mfb_lows == 0U && !m.mfb);
    assert(m.delayed_ms == 0U);

    /* Every normal command is serialized until its Command_ACK arrives. */
    assert(bm83_request_now_playing_metadata(&dev, 0U) == DEV_EBUSY);
    const uint8_t command_ack[] = {0xAA,0x00,0x03,0x00,0x04,0x00,0xF9};
    bm83_rx_data(&dev, command_ack, sizeof(command_ack));
    assert(!dev.awaiting_command_ack);

    assert(bm83_read_paired_device_record(&dev) == DEV_OK);
    const uint8_t expected_paired_read[] = {0xAA,0x00,0x02,0x0E,0x00,0xF0};
    assert(m.frame_len == sizeof(expected_paired_read));
    assert(memcmp(m.frame, expected_paired_read, sizeof(expected_paired_read)) == 0);
    const uint8_t paired_ack[] = {0xAA,0x00,0x03,0x00,0x0E,0x00,0xEF};
    bm83_rx_data(&dev, paired_ack, sizeof(paired_ack));
    const uint8_t paired_reply[] = {
        0xAA,0x00,0x10,0x1F,0x02,
        0x02,0x66,0x55,0x44,0x33,0x22,0x11,
        0x01,0xA6,0xA5,0xA4,0xA3,0xA2,0xA1,
        0x92
    };
    bm83_rx_data(&dev, paired_reply, sizeof(paired_reply));
    assert(g_bm83_diag.paired_device_count == 2U);
    assert(g_bm83_diag.paired_newest_valid == 1U);
    const uint8_t newest_addr[] = {0xA6,0xA5,0xA4,0xA3,0xA2,0xA1};
    assert(memcmp((const void *)g_bm83_diag.paired_newest_address,
                  newest_addr, sizeof(newest_addr)) == 0);
    assert(dev.paired_device_count == 2U);
    assert(dev.paired_newest_valid);
    assert(dev.paired_newest_record_index == 1U);
    assert(memcmp(dev.paired_newest_address, newest_addr, sizeof(newest_addr)) == 0);

    assert(bm83_link_back_address_a2dp(&dev, 1U, newest_addr) == DEV_OK);
    const uint8_t expected_address_back[] = {
        0xAA,0x00,0x0A,0x17,0x05,0x01,0x04,
        0xA6,0xA5,0xA4,0xA3,0xA2,0xA1,0x00
    };
    assert(m.frame_len == sizeof(expected_address_back));
    assert(memcmp(m.frame, expected_address_back, sizeof(expected_address_back)) == 0);
    const uint8_t address_back_ack[] = {0xAA,0x00,0x03,0x00,0x17,0x00,0xE6};
    bm83_rx_data(&dev, address_back_ack, sizeof(address_back_ack));

    assert(bm83_set_supported_classic_profiles(
               &dev,
               (uint8_t)(BM83_PROFILE_A2DP | BM83_PROFILE_AVRCP_CT | BM83_PROFILE_AVRCP_TG)) == DEV_OK);
    const uint8_t expected_profiles[] = {0xAA,0x00,0x03,0x07,0x04,0x1C,0xD6};
    assert(m.frame_len == sizeof(expected_profiles));
    assert(memcmp(m.frame, expected_profiles, sizeof(expected_profiles)) == 0);
    const uint8_t profiles_ack[] = {0xAA,0x00,0x03,0x00,0x07,0x00,0xF6};
    bm83_rx_data(&dev, profiles_ack, sizeof(profiles_ack));
    assert(!dev.awaiting_command_ack);

    assert(bm83_toggle_audio_source(&dev) == DEV_OK);
    const uint8_t expected_toggle[] = {0xAA,0x00,0x02,0xCC,0x01,0x31};
    assert(m.frame_len == sizeof(expected_toggle));
    assert(memcmp(m.frame, expected_toggle, sizeof(expected_toggle)) == 0);
    const uint8_t toggle_ack[] = {0xAA,0x00,0x03,0x00,0xCC,0x00,0x31};
    bm83_rx_data(&dev, toggle_ack, sizeof(toggle_ack));
    assert(!dev.awaiting_command_ack);

    assert(bm83_read_eeprom(&dev, 0x1234U, 16U) == DEV_OK);
    const uint8_t expected_read[] = {0xAA,0x00,0x04,0x3C,0x12,0x34,0x10,0x6A};
    assert(m.frame_len == sizeof(expected_read));
    assert(memcmp(m.frame, expected_read, sizeof(expected_read)) == 0);
    const uint8_t read_ack[] = {0xAA,0x00,0x03,0x00,0x3C,0x00,0xC1};
    bm83_rx_data(&dev, read_ack, sizeof(read_ack));
    assert(!dev.awaiting_command_ack);

    assert(bm83_read_link_status(&dev) == DEV_OK);
    const uint8_t expected_link[] = {0xAA,0x00,0x02,0x0D,0x00,0xF1};
    assert(m.frame_len == sizeof(expected_link));
    assert(memcmp(m.frame, expected_link, sizeof(expected_link)) == 0);
    const uint8_t link_ack[] = {0xAA,0x00,0x03,0x00,0x0D,0x00,0xF0};
    bm83_rx_data(&dev, link_ack, sizeof(link_ack));
    assert(!dev.awaiting_command_ack);

    assert(bm83_read_remote_avrcp_features(&dev, 0U) == DEV_OK);
    const uint8_t expected_avrcp_features[] = {0xAA,0x00,0x03,0x16,0x00,0x03,0xE4};
    assert(m.frame_len == sizeof(expected_avrcp_features));
    assert(memcmp(m.frame, expected_avrcp_features, sizeof(expected_avrcp_features)) == 0);
    const uint8_t avrcp_info_ack[] = {0xAA,0x00,0x03,0x00,0x16,0x00,0xE7};
    bm83_rx_data(&dev, avrcp_info_ack, sizeof(avrcp_info_ack));
    assert(!dev.awaiting_command_ack);
    const uint8_t avrcp_info[] = {0xAA,0x00,0x04,0x17,0x00,0x03,0x01,0xE1};
    bm83_rx_data(&dev, avrcp_info, sizeof(avrcp_info));
    assert(g_bm83_diag.remote_avrcp_features_valid == 1U);
    assert(g_bm83_diag.remote_avrcp_features == 0x01U);

    assert(bm83_link_back_last_device(&dev) == DEV_OK);
    const uint8_t expected_link_back[] = {0xAA,0x00,0x02,0x17,0x00,0xE7};
    assert(m.frame_len == sizeof(expected_link_back));
    assert(memcmp(m.frame, expected_link_back, sizeof(expected_link_back)) == 0);
    const uint8_t link_back_ack[] = {0xAA,0x00,0x03,0x00,0x17,0x00,0xE6};
    bm83_rx_data(&dev, link_back_ack, sizeof(link_back_ack));
    assert(!dev.awaiting_command_ack);

    assert(bm83_link_back_last_a2dp(&dev) == DEV_OK);
    const uint8_t expected_a2dp_back[] = {0xAA,0x00,0x02,0x17,0x02,0xE5};
    assert(m.frame_len == sizeof(expected_a2dp_back));
    assert(memcmp(m.frame, expected_a2dp_back, sizeof(expected_a2dp_back)) == 0);
    bm83_rx_data(&dev, link_back_ack, sizeof(link_back_ack));
    assert(!dev.awaiting_command_ack);

    assert(bm83_request_now_playing_metadata(&dev, 0U) == DEV_OK);
    const uint8_t expected_metadata[] = {
        0xAA,0x00,0x13,0x0B,0x00,0x20,0x00,0x00,0x0D,
        0x00,0x00,0x00,0x00,0x00,0x00,0x00,0x00,0x01,
        0x00,0x00,0x00,0x01,0xB3,
    };
    assert(m.frame_len == sizeof(expected_metadata));
    assert(memcmp(m.frame, expected_metadata, sizeof(expected_metadata)) == 0);
    const uint8_t metadata_ack[] = {0xAA,0x00,0x03,0x00,0x0B,0x00,0xF2};
    bm83_rx_data(&dev, metadata_ack, sizeof(metadata_ack));
    assert(!dev.awaiting_command_ack);

    assert(bm83_register_track_changed(&dev, 0U) == DEV_OK);
    const uint8_t expected_track_notify[] = {
        0xAA,0x00,0x0B,0x0B,0x00,0x31,0x00,0x00,0x05,
        0x02,0x00,0x00,0x00,0x00,0xB2
    };
    assert(m.frame_len == sizeof(expected_track_notify));
    assert(memcmp(m.frame, expected_track_notify, sizeof(expected_track_notify)) == 0);
    bm83_rx_data(&dev, metadata_ack, sizeof(metadata_ack));
    assert(!dev.awaiting_command_ack);

    assert(bm83_request_event_capabilities(&dev, 0U) == DEV_OK);
    const uint8_t expected_caps[] = { 0xAA,0x00,0x07,0x0B,0x00,0x10,0x00,0x00,0x01,0x03,0xDA };
    assert(m.frame_len == sizeof(expected_caps));
    assert(memcmp(m.frame, expected_caps, sizeof(expected_caps)) == 0);
    bm83_rx_data(&dev, metadata_ack, sizeof(metadata_ack));
    assert(!dev.awaiting_command_ack);

    assert(bm83_request_now_playing_attribute(&dev, 0U, 2U) == DEV_OK);
    assert(m.frame_len == sizeof(expected_metadata));
    assert(m.frame[21] == 0x02U);
    bm83_rx_data(&dev, metadata_ack, sizeof(metadata_ack));
    assert(!dev.awaiting_command_ack);

    assert(bm83_request_now_playing_attribute(&dev, 0U, 3U) == DEV_OK);
    assert(m.frame_len == sizeof(expected_metadata));
    assert(m.frame[21] == 0x03U);
    bm83_rx_data(&dev, metadata_ack, sizeof(metadata_ack));
    assert(!dev.awaiting_command_ack);

    assert(bm83_request_current_metadata_v206(&dev, 0U) == DEV_OK);
    assert(m.frame[3] == BM83_CMD_AVRCP_VENDOR_DEPENDENT);
    assert(m.frame[4] == 0x00U && m.frame[5] == 0x20U && m.frame[6] == 0x03U);
    assert(m.frame[10] == 0x01U && m.frame[14] == 0x02U && m.frame[18] == 0x03U);
    const uint8_t modern_ack[] = {0xAA,0x00,0x03,0x00,0x4A,0x00,0xB3};
    bm83_rx_data(&dev, modern_ack, sizeof(modern_ack));
    assert(!dev.awaiting_command_ack);

    assert(bm83_request_current_metadata_attribute_v206(&dev, 0U, 7U) == DEV_OK);
    assert(m.frame[3] == BM83_CMD_AVRCP_VENDOR_DEPENDENT);
    assert(m.frame[4] == 0x00U && m.frame[5] == 0x20U && m.frame[6] == 0x01U);
    assert(m.frame[10] == 0x07U);
    bm83_rx_data(&dev, modern_ack, sizeof(modern_ack));
    assert(!dev.awaiting_command_ack);

    assert(bm83_request_media_player_list(&dev, 0U) == DEV_OK);
    assert(m.frame[3] == BM83_CMD_AVRCP_BROWSING);
    assert(m.frame[4] == 0x00U && m.frame[5] == 0x00U && m.frame[6] == 0x00U);
    assert(m.frame[14] == 0x00U && m.frame[15] == 0x00U);
    const uint8_t browse_ack[] = {0xAA,0x00,0x03,0x00,0x41,0x00,0xBC};
    bm83_rx_data(&dev, browse_ack, sizeof(browse_ack));
    assert(!dev.awaiting_command_ack);

    assert(bm83_set_addressed_player(&dev, 0U, 0x1234U) == DEV_OK);
    assert(m.frame[3] == BM83_CMD_AVRCP_BROWSING);
    assert(m.frame[4] == 0x02U && m.frame[5] == 0x00U &&
           m.frame[6] == 0x12U && m.frame[7] == 0x34U);
    bm83_rx_data(&dev, browse_ack, sizeof(browse_ack));
    assert(!dev.awaiting_command_ack);

    assert(bm83_set_browsed_player(&dev, 0U, 0x1234U) == DEV_OK);
    assert(m.frame[3] == BM83_CMD_AVRCP_BROWSING);
    assert(m.frame[4] == 0x03U && m.frame[5] == 0x00U &&
           m.frame[6] == 0x12U && m.frame[7] == 0x34U);
    bm83_rx_data(&dev, browse_ack, sizeof(browse_ack));
    assert(!dev.awaiting_command_ack);

    assert(bm83_request_now_playing_browse(&dev, 0U) == DEV_OK);
    const uint8_t expected_browse[] = {
        0xAA,0x00,0x19,0x41,0x00,0x00,0x03,
        0x00,0x00,0x00,0x00,0x00,0x00,0x00,0x00,0x03,
        0x00,0x00,0x00,0x01,0x00,0x00,0x00,0x02,
        0x00,0x00,0x00,0x03,0x9A
    };
    assert(m.frame_len == sizeof(expected_browse));
    assert(memcmp(m.frame, expected_browse, sizeof(expected_browse)) == 0);
    bm83_rx_data(&dev, browse_ack, sizeof(browse_ack));
    assert(!dev.awaiting_command_ack);

    const uint8_t track_uid[8] = {0x01,0x23,0x45,0x67,0x89,0xAB,0xCD,0xEF};
    assert(bm83_request_item_attributes(&dev, 0U, 0x03U, track_uid, 0x1357U) == DEV_OK);
    assert(m.frame[3] == BM83_CMD_AVRCP_BROWSING);
    assert(m.frame[4] == 0x05U && m.frame[5] == 0x00U && m.frame[6] == 0x03U);
    assert(memcmp(&m.frame[7], track_uid, sizeof(track_uid)) == 0);
    assert(m.frame[15] == 0x13U && m.frame[16] == 0x57U);
    assert(m.frame[17] == 0x07U);
    assert(m.frame[21] == 0x01U && m.frame[25] == 0x02U && m.frame[29] == 0x03U);
    assert(m.frame[33] == 0x04U && m.frame[37] == 0x05U && m.frame[41] == 0x06U &&
           m.frame[45] == 0x07U);
    bm83_rx_data(&dev, browse_ack, sizeof(browse_ack));
    assert(!dev.awaiting_command_ack);

    packet_capture_t cap = {0};
    bm83_set_packet_callback(&dev, packet_cb, &cap);
    const uint8_t event[] = {0xAA,0x00,0x03,0x01,0x06,0x00,0xF6};
    unsigned writes_before = m.writes;
    bm83_rx_data(&dev, event, sizeof(event));
    assert(cap.calls == 1U);
    assert(cap.packet.id == BM83_EVENT_BTM_STATUS);
    assert(cap.packet.payload_len == 2U && cap.packet.payload[0] == 0x06U);
    assert(m.writes == writes_before + 1U); /* Event_ACK */
    const uint8_t expected_ack[] = {0xAA,0x00,0x02,0x14,0x01,0xE9};
    assert(m.frame_len == sizeof(expected_ack));
    assert(memcmp(m.frame, expected_ack, sizeof(expected_ack)) == 0);

    /* Missing ACK: retry the exact frame at 200 ms, then follow the documented
     * hardware reset sequence after a second 200 ms timeout. */
    bm_mock_t retry = {0};
    dev_uart_bus_t retry_uart = { .ctx = &retry, .write = mock_uart_write };
    dev_gpio_t retry_mfb = { .ctx = &retry, .write = mock_gpio_write };
    dev_gpio_t retry_reset = { .ctx = &retry, .write = mock_reset_write };
    dev_clock_t retry_clock = { .ctx = &retry, .delay_ms = mock_delay, .time_ms = mock_time };
    bm83_t retry_dev;
    assert(bm83_init(&retry_dev, &retry_uart, &retry_reset, &retry_mfb, NULL, &retry_clock) == DEV_OK);
    assert(bm83_music_control(&retry_dev, BM83_MUSIC_NEXT) == DEV_OK);
    const unsigned first_writes = retry.writes;
    retry.now_ms += BM83_COMMAND_ACK_TIMEOUT_MS;
    assert(bm83_service(&retry_dev) == DEV_EBUSY);
    assert(retry.writes == first_writes + 1U);
    retry.now_ms += BM83_COMMAND_ACK_TIMEOUT_MS;
    assert(bm83_service(&retry_dev) == DEV_ETIMEOUT);
    assert(retry.reset_lows == 1U && retry.reset_highs == 1U);
    assert(!retry_dev.awaiting_command_ack);

    /* Metadata is auxiliary to A2DP. Losing both ACK attempts for an AVRCP
     * query must abandon that query without resetting a healthy streaming
     * BM83; a later poll may retry it. */
    bm_mock_t metadata_retry = {0};
    dev_uart_bus_t metadata_uart = { .ctx = &metadata_retry, .write = mock_uart_write };
    dev_gpio_t metadata_mfb = { .ctx = &metadata_retry, .write = mock_gpio_write };
    dev_gpio_t metadata_reset = { .ctx = &metadata_retry, .write = mock_reset_write };
    dev_clock_t metadata_clock = {
        .ctx = &metadata_retry, .delay_ms = mock_delay, .time_ms = mock_time
    };
    bm83_t metadata_dev;
    assert(bm83_init(&metadata_dev, &metadata_uart, &metadata_reset,
                     &metadata_mfb, NULL, &metadata_clock) == DEV_OK);
    assert(bm83_request_current_metadata_attribute_v206(&metadata_dev, 0U, 1U) == DEV_OK);
    unsigned metadata_writes = metadata_retry.writes;
    metadata_retry.now_ms += BM83_COMMAND_ACK_TIMEOUT_MS;
    assert(bm83_service(&metadata_dev) == DEV_EBUSY);
    assert(metadata_retry.writes == metadata_writes + 1U);
    metadata_retry.now_ms += BM83_COMMAND_ACK_TIMEOUT_MS;
    assert(bm83_service(&metadata_dev) == DEV_EBUSY);
    assert(!metadata_dev.awaiting_command_ack);
    assert(metadata_retry.reset_lows == 0U && metadata_retry.reset_highs == 0U);
    assert(g_bm83_diag.command_timeout_count == 1U);
    assert(g_bm83_diag.nonfatal_command_timeout_count == 1U);

    /* Explicit BM83 Busy/Memory Full on an auxiliary 0x4A query is a
     * readiness handshake, not a timer-based retry. The exact command is gated
     * until the later matching status-0 ACK while unrelated controls still work. */
    bm_mock_t busy = {0};
    dev_uart_bus_t busy_uart = { .ctx = &busy, .write = mock_uart_write };
    dev_clock_t busy_clock = { .ctx = &busy, .time_ms = mock_time };
    bm83_t busy_dev;
    assert(bm83_init(&busy_dev, &busy_uart, NULL, NULL, NULL, &busy_clock) == DEV_OK);
    uint32_t busy_before = g_bm83_diag.nonfatal_busy_ack_count;
    uint32_t ready_before = g_bm83_diag.nonfatal_ready_ack_count;
    assert(bm83_request_current_metadata_v206(&busy_dev, 0U) == DEV_OK);
    const uint8_t memory_full_ack[] = {0xAA,0x00,0x03,0x00,0x4A,0x05,0xAE};
    bm83_rx_data(&busy_dev, memory_full_ack, sizeof(memory_full_ack));
    assert(!busy_dev.awaiting_command_ack);
    assert(bm83_command_waiting_ready(&busy_dev, BM83_CMD_AVRCP_VENDOR_DEPENDENT));
    assert(g_bm83_diag.nonfatal_busy_ack_count == busy_before + 1U);
    unsigned busy_writes = busy.writes;
    busy.now_ms += BM83_COMMAND_ACK_TIMEOUT_MS;
    assert(bm83_service(&busy_dev) == DEV_OK);
    assert(busy.writes == busy_writes);
    assert(bm83_request_current_metadata_v206(&busy_dev, 0U) == DEV_EBUSY);
    assert(busy.writes == busy_writes);

    assert(bm83_music_control(&busy_dev, BM83_MUSIC_PLAY) == DEV_OK);
    assert(busy_dev.awaiting_command_ack);
    assert(busy_dev.pending_command_id == BM83_CMD_MUSIC_CONTROL);

    /* Deliver readiness while the unrelated control still awaits its own ACK.
     * Matching by command ID must clear only the metadata gate. */
    const uint8_t ready_ack[] = {0xAA,0x00,0x03,0x00,0x4A,0x00,0xB3};
    bm83_rx_data(&busy_dev, ready_ack, sizeof(ready_ack));
    assert(!bm83_command_waiting_ready(&busy_dev, BM83_CMD_AVRCP_VENDOR_DEPENDENT));
    assert(g_bm83_diag.nonfatal_ready_ack_count == ready_before + 1U);
    assert(busy_dev.awaiting_command_ack);
    assert(busy_dev.pending_command_id == BM83_CMD_MUSIC_CONTROL);

    const uint8_t play_ack[] = {0xAA,0x00,0x03,0x00,0x04,0x00,0xF9};
    bm83_rx_data(&busy_dev, play_ack, sizeof(play_ack));
    assert(!busy_dev.awaiting_command_ack);
    assert(bm83_request_current_metadata_v206(&busy_dev, 0U) == DEV_OK);

    /* A fielded BM83 v2.02 build can omit the documented delayed readiness ACK.
     * After a long quiet interval the driver must permit exactly one new probe,
     * not auto-transmit and not enter a fixed-rate retry loop. */
    bm_mock_t fallback = {0};
    dev_uart_bus_t fallback_uart = { .ctx = &fallback, .write = mock_uart_write };
    dev_clock_t fallback_clock = { .ctx = &fallback, .time_ms = mock_time };
    bm83_t fallback_dev;
    assert(bm83_init(&fallback_dev, &fallback_uart, NULL, NULL, NULL,
                     &fallback_clock) == DEV_OK);
    uint32_t ready_timeout_before = g_bm83_diag.nonfatal_ready_timeout_count;
    assert(bm83_request_current_metadata_v206(&fallback_dev, 0U) == DEV_OK);
    bm83_rx_data(&fallback_dev, memory_full_ack, sizeof(memory_full_ack));
    assert(bm83_command_waiting_ready(&fallback_dev,
                                      BM83_CMD_AVRCP_VENDOR_DEPENDENT));
    unsigned fallback_writes = fallback.writes;
    fallback.now_ms += BM83_NONFATAL_READY_TIMEOUT_MS - 1U;
    assert(bm83_service(&fallback_dev) == DEV_OK);
    assert(bm83_command_waiting_ready(&fallback_dev,
                                      BM83_CMD_AVRCP_VENDOR_DEPENDENT));
    assert(fallback.writes == fallback_writes);

    fallback.now_ms += 1U;
    assert(bm83_service(&fallback_dev) == DEV_OK);
    assert(!bm83_command_waiting_ready(&fallback_dev,
                                       BM83_CMD_AVRCP_VENDOR_DEPENDENT));
    assert(g_bm83_diag.nonfatal_ready_timeout_count == ready_timeout_before + 1U);
    assert(fallback.writes == fallback_writes);
    assert(bm83_request_current_metadata_v206(&fallback_dev, 0U) == DEV_OK);
    assert(fallback.writes == fallback_writes + 1U);
}
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
