ProccyBoi/kiku/Mechanical/scripts/build_housing.py

"""Parametric Kiku enclosure prototype.

The coordinate system follows Mechanical/reference/board_datums.json:
X = 0..60 mm left-to-right across the PCB, Y = 0..105 mm bottom-to-top,
Z = 0 mm at the PCB rear face and Z = 1.6 mm at the PCB front face.

This is intentionally a first-print enclosure, not a frozen mould-tool model.  The
battery, LCD stack adhesive, FM coax bend and kickstand fit remain parameters so
they can be corrected after physical fit checks without redrawing the housing.
"""

from pathlib import Path
import json
import math

import cadquery as cq
import trimesh


ROOT = Path(__file__).resolve().parents[2]
MECH = ROOT / "Mechanical"
OUT = MECH / "exports"
REVIEW = MECH / "review"
DATUMS = MECH / "reference" / "board_datums.json"
PCB_STEP = MECH / "reference" / "pcb_populated.step"

OUT.mkdir(parents=True, exist_ok=True)
REVIEW.mkdir(parents=True, exist_ok=True)


# -----------------------------------------------------------------------------
# Primary product parameters (mm)
# -----------------------------------------------------------------------------
PCB_W = 60.0
PCB_H = 105.0
PCB_T = 1.6

CASE_W = 69.0
CASE_H = 115.0
CASE_CX = PCB_W / 2.0
CASE_CY = PCB_H / 2.0
CASE_R = 11.0
WALL = 1.8

# V8 appearance-first envelope.  The 10 mm battery is absorbed into a uniformly
# deeper rear shell instead of a local hump, producing one continuous back surface.
REAR_Z0 = -13.5
REAR_BACK_WALL = 3.0
SEAM_Z = 0.5
SEAM_GAP = 0.12
FRONT_Z1 = 15.2

# Display from HS20HS072RX mechanical drawing / current KiCad placement.
LCD_CX = 30.01
LCD_CY = 82.885
LCD_BODY_W = 51.8
LCD_BODY_H = 36.2
LCD_ACTIVE_W = 40.8
LCD_ACTIVE_H = 30.6
LENS_W = 54.0
LENS_H = 39.6
LENS_R = 5.8
LENS_T = 0.8

# Current PCB controls.
BTN1 = (16.0, 55.0)
BTN2 = (44.0, 55.0)
ENC = (30.0, 40.0)

# V8 control language: two soft "pebble" button caps and a rounded encoder puck.
# The button caps are installed from the outside after the PCB/front shell are in
# place.  A split square socket grips the real 7.2 x 7.2 mm actuator on SW3/SW4,
# rather than relying on gravity or a loose centre stem.  The slight interference
# is intentional and the split socket provides compliance for PA12/FDM prototypes.
BUTTON_APERTURE = 10.4
BUTTON_HEAD_W = 14.0
BUTTON_HEAD_H = 11.6
BUTTON_HEAD_Z0 = FRONT_Z1 - 0.05
BUTTON_HEAD_Z1 = FRONT_Z1 + 2.85
BUTTON_SOCKET_OUTER = 9.4
BUTTON_SOCKET_INNER = 7.05
BUTTON_SOCKET_Z0 = 12.0
BUTTON_SOCKET_Z1 = BUTTON_HEAD_Z0 + 0.15
BUTTON_SOCKET_ROOF_Z = 13.72
BUTTON_SOCKET_SPLIT = 0.65
BUTTON_LEFT_ANGLE = -7.0
BUTTON_RIGHT_ANGLE = 7.0
BUTTON_RECESS_W = 15.2
BUTTON_RECESS_H = 12.8
BUTTON_RECESS_DEPTH = 0.60
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
